pjerus/Temporal-Replay-26-Badge/docs/checkpoints/2026-10-08.md

# Checkpoint 2026-10-08

Parts shopping for driving Rocky's five LEGO Power Functions motors from the spare badge. No code changed; all work is on one page in rocky-robot. Paused for a reboot.

## Completed this session
- `~/ai-dev/rocky-robot/docs/hardware/pf-motor-parts.html`, committed there on `tread-drive` as d530e94, not pushed:
  - "What to buy": four costed options for the motors on hand (three M, one L, one XL) and two shopping lists.
  - Soldered pick, chosen on price: one Adafruit FeatherWing (M and L motors) plus one Pololu Motoron (XL), $44.90 for boards, $70.35 whole build, plus a soldering iron ($17.54 at Anchor).
  - No-soldering build: three Pololu Motorons with screw-down barrier strips, $112.43.
  - Folded table of every part and source checked: SparkFun, Pololu, Anchor Electronics, Jameco, Micro Center Santa Clara, and three Bangkok shops (baht and dollars at 33.3), with soldering tags and riser posts for Technic beams.
  - Parts on hand now lists three Power Functions extension wires (8886).
- Found: no local store has an I2C motor board on the shelf. Jameco boards ship 22 October. Bangkok has no Motoron; Arduitronics has a 290 baht I2C shield.

## Open PRs
None.

## Open issues
None assigned.

## In-flight branches
- `pocket-scanner-phase2` (this repo): de0d811 plus this checkpoint, 7 ahead of `backup` before it, not pushed. Untracked and left alone: `arduino-cli.yaml`, `backups/`.
- rocky-robot `tread-drive`: d530e94, not pushed. The five D11 face-retry files are still uncommitted there, untouched this session.

## Workers/processes to restart on resume
- None from this session: no code changed and nothing was left running.
- The Mac is being rebooted, so anything that was running before stops. Carried over from 7 October: Rocky's brain on the Mac needs a start, and it still lacks the uncommitted D11 retry. The Pi services were not touched.

## Known faults and open questions
- Pat has not chosen between the soldered and the no-soldering build. He has no soldering iron.
- Nothing on the page is tested on hardware: Technic hole fit for the riser posts, the Motoron's motor pins taking push-on jumpers, the XL's current through thin jumper wires.
- Not confirmed: Anchor shelf stock, the badge port's pin order on the ECHO board, whether the Bangkok shield arrives with pins fitted, whether Arduitronics or ThaiEasyElec take walk-in customers.
- Jameco and Micro Center block the headless browser; Firecrawl was used (about 815 credits left, period ends 1 November).

## Next steps
1. Pat picks a build; then order boards (Pololu, and Micro Center if the FeatherWing) and phone Anchor on (408) 727-3693 before the trip.
2. Cut one extension wire and check both halves fit a motor before cutting the other two.
3. Meter-check the badge's 4-pin port, then carry on with the 7 October list (commit D11 retry, restart Rocky, test at the robot).
