pjerus/Temporal-Replay-26-Badge/docs/checkpoints/2026-10-07.md

# Checkpoint 2026-10-07

Rocky's body: the LEGO tank base is driven from rocky-pi through the spare badge. The move-feedback build is done on the Mac but only half deployed to the Pi.

## Completed this session
- On-badge DRIVE app (b83064a) and HELI app for the Syma S107G (1e47bba); both badges carry both apps. Spare = "Rocky IR Tread" (env `echo-drive`), face = "Rocky Face" (env `echo-face-drive`).
- rocky-pi drives the treads: brain → `rocky-body` (8027) → `emotion-bridge` (8026) → spare badge → IR. Proven on the base (forward, early stop, replace).
- Body-feedback design, rev 1: `docs/superpowers/specs/rocky-body-feedback-design.html` (a41de7a). Tread-drive design at rev 3 (f183a66).
- Feedback build, all on `tread-drive` and not pushed:
  - pi-arduino-face-emotions: 4be09ac, 73c4b83 (move ids, endings, `recent_moves`, `refused`), ec45a3e (BLE deadlines), b8734db (history when the badge is gone), b04b188 (`start_within_ms`). 152 tests pass.
  - rocky-robot: 68e1d6a … b2fa2f8 (`schema: 2`, `senses`, drive passthrough, 409 on refusal). 919 tests pass.
- Tested on the base with the first deploy (4be09ac + 73c4b83 level): finished, stopped and replaced endings all reported correctly.
- Name Flip setting (3a947bb): `name_flip = 1` stops the name screen turning on a badge that senses itself inverted. Flashed to the spare and switched on there; Pat confirmed it reads correctly.
- `~/.rocky/config.toml` has `body_enabled = true`; Keychain item `rocky-pi-body` holds the body key.

## Open PRs
None.

## Open issues
None assigned.

## In-flight branches
- `pocket-scanner-phase2` (this repo): 3a947bb, two commits ahead of `backup` (a41de7a, 3a947bb). Push goes to `backup`, never `origin`.
- `tread-drive` in pi-arduino-face-emotions and rocky-robot: unpushed, unmerged, and the Pi runs them.

## Workers/processes to restart on resume
- **rocky-pi `emotion-bridge` and `rocky-body`** — still on the first feedback deploy (services last restarted 05:46 BST on 2026-10-07). They lack ec45a3e, b8734db, b04b188 and the matching rocky-robot commits. Deploy both together: Pat runs `bash ~/ai-dev/pi-arduino/.superpowers/pi_deploy_feedback.sh` (Claude cannot write to the Pi). A second run reported by Pat changed nothing; cause unknown. Check with `grep -c start_within_ms` in the installed `bridge.py`.
- Rocky Face may need switching off and on after the bridge restarts.
- Rocky Face firmware does not have 3a947bb (not needed unless mounted the same way).
- Rocky (the Mac brain) must not run the new client against the old Pi services; deploy the Pi first.

## Known faults and open questions
- Switch-off test not yet passed: with the old Pi code the bridge hung when the badge dropped and the move was never marked `lost`. Fixed in code, unproven on hardware.
- First move after a cold reconnect is refused (connect about 2.6 s, start limit 1 s). Honest answer, brain can retry.
- Spare's battery reads 0 % or 100 %; neither is trusted.
- A badge with its own Drive app open ignores BLE commands silently; needs a firmware flag.
- The BLE secret is hard-coded in firmware and sent unencrypted.
- HELI: stick and trim directions untested (helicopter battery was flat); sent/failed counter still on screen.
- Design page needs a revision recording the build's corrections (deadlines, `recent_moves`, `refused`, `start_within_ms`).

## Next steps
1. Pat reruns the Pi deploy script; confirm both services restarted and hold the new code.
2. Rerun the switch-off test on the base: expect `lost` / `unreachable` about three seconds after the badge goes off, with the history still readable.
3. Revise the feedback design page, then ask Pat about pushing the three branches.

## 12:08 update

The switch-off test passed on the base, a late-`lost` fault was found and fixed, and all three projects are pushed.

### Completed
- Pi deploy of the feedback build confirmed, then redeployed with the fix. rocky-pi `emotion-bridge` restarted 19:56:36 BST and `rocky-body` 19:56:42 BST on 2026-10-07; both run the merged code below.
- Fault found on the base: a status poll saw the badge gone at 1.9 s but the move stayed `running` until 13.5 s. Fixed in pi-arduino-face-emotions 82fb069 (a move is lost the moment anything finds the badge gone). Intermittent on the old code (a race), so the unit test is the main proof.
- Three chained runs on the fix, four drops, each `lost/unreachable` in the same poll as `reachable=false`. Reconnect moves accepted first try.
- Feedback design page at revision 2 (72fcf41): corrections C1–C6, results table, open points.
- rocky-robot 02384db: Rocky calls his face his face, never a screen (done by the rocky-robot session).
- Merged and pushed: pi-arduino-face-emotions `main` = `tread-drive` = 82fb069; rocky-robot `main` = `tread-drive` = 02384db (fast-forwards, 153 and 919 tests pass). This repo: `pocket-scanner-phase2` pushed to `backup` at 72fcf41, not merged to `main`.
- Manifest checksum committed (5fa52ae).
- `.superpowers/pi_deploy_feedback.sh` (git-ignored) now drops the Pi's Bluetooth links to the badges before restarting the bridge. Untried.

### Open PRs / issues
None.

### In-flight branches
- `pocket-scanner-phase2`: level with `backup`. `main` follows upstream (34 commits this branch lacks, 106 it has); merging is Pat's decision. Never push to `origin`.

### Workers/processes to restart on resume
- None owed. Both Pi services run the pushed code.
- Rocky (the Mac brain) was started before 02384db; restart it to pick up the face wording.
- After any future bridge restart, Rocky Face may need switching off and on unless the new link-drop step in the deploy script works.

### Known faults and open questions
- Rocky's brain does not read the tread report (`BodySense` reads touch and distance only), so a lost move is reported by the body and heard by nobody.
- Brick reports pan and tilt as not homed; poses answer 409 until Pat confirms the joints are at home and `POST /home` is sent.
- Body service caps a move at 5000 ms (`[drive] max_ms`); longer drives are chained moves.
- Earlier items still open: Drive app open on the badge ignores BLE silently; BLE secret hard-coded; spare's battery reading; HELI untested.

### Next steps
1. Have Rocky's brain read `drive` (reachable, `last_move`, `recent_moves`) so it hears a lost or refused move.
2. Home pan and tilt with Pat at the robot.
3. On the next Pi deploy, check whether the link-drop step removes the need to power-cycle Rocky Face.

## 13:20 update

Three more bridge changes went to the Pi, Rocky now feels his legs, and an ESP32 modules research page was written.

### Completed
- Bridge (pi-arduino-face-emotions, `main` = `tread-drive` = adf98f3, pushed): a886e74 (a badge that goes off is reported gone without extra waits: the two slow cases of 7 s and 11 s), adf98f3 (a mood for a badge that is away answers at once). 158 tests pass.
- rocky-robot `main` = `tread-drive` = 85db420, pushed: Rocky feels his legs (2d78087, done by the rocky-robot session). Shown live for legs gone and back. 941 tests pass.
- Pi: both services restarted 21:11:37 / 21:11:43 BST on 2026-10-07 and run adf98f3.
- Deploy script's link-drop step worked once (21:11 deploy, face badge left alone, moods answered).
- Feedback design page at revision 3 (5e9e80c): corrections C7–C9, "later the same evening" table, updated open points.
- ESP32 modules research: `rocky-robot/docs/hardware/esp32-modules.html` (130 modules, 13 function groups, scrolling tree, 11-family table) and `esp32-modules-notes/` (three helper reports, chip and satellite facts). Untracked there; Pat has not reviewed it. Registry has a Research entry.
- New global rule `~/.claude/rules/subagent-sizing.md` (model per agent, Kev for bigger jobs, one-tier upgrades, no sub-spawning), after the research job spent about 20 million tokens on four full-size agents.

### Open PRs / issues
None.

### In-flight branches
- `pocket-scanner-phase2`: 5e9e80c plus this checkpoint, ahead of `backup` (d60a386). `main` still unmerged by choice.

### Workers/processes to restart on resume
- None owed. The Pi runs the pushed bridge and body code.
- Rocky (the Mac brain) was last restarted 12:52 Mac time on 85db420's parent code; restart it if rocky-robot changes again.

### Known faults and open questions
- C7–C9 (slow switch-off fixes, fast face failure) are deployed but untried on the base.
- Rocky not yet seen to hear a move lost while one runs, nor the face moods for legs events.
- Switch-on delay of 10–25 s is unmeasured; likely the badge's start-up before it advertises.
- Arm on the Pi is the pretend controller by intent ("we haven't reached that build phase yet").
- Mood sequences lack the fast-failure short cut.

### Next steps
1. With Pat at the robot: switch Rocky Face off and on (fast face failure), then the tread badge off (expect Rocky to notice within about 3 s).
2. Pat reads the ESP32 modules page; trim or deepen, then commit it in rocky-robot and link it from the parts guide. Follow-up research under the sizing rule.
3. Time the switch-on delay: badge menu appearing versus `reachable` turning true.

## 13:22 update

Only change since the update above: everything is pushed.

### Completed
- `pocket-scanner-phase2` pushed to `backup` at 1a17062 (design page revision 3, checkpoint).

### Open PRs / issues
None open by me.

### In-flight branches
- `pocket-scanner-phase2`: level with `backup` apart from this note. `main` (f140554) still unmerged by choice.
- Untracked and left alone: `arduino-cli.yaml`, `backups/`.

### Workers/processes to restart on resume
- None. No code changed since the Pi's 21:11 BST restart.

### Next steps
Unchanged: the three in the update above.

## 16:07 update

### Completed
- `rocky-body-feedback-design.html` is at revision 4 (8f611f1, c9341ac, 5a07617, 5b52422, 97476a2). It records the rocky-robot session's results for C7 to C9 on the base, about 22:25 to 22:47 BST (14:25 to 14:47 Mac time):
  - Face badge off and on (C9): pass. Moods failed in 0.05 to 0.14 s while off; first good one after switch-on took 0.35 s.
  - Tread badge off mid-move (C6 to C8): pass, three times. Each lost move was marked lost in the report that first showed the badge gone; slowest report 1.17 s; no 7 s or 11 s silence.
  - One miss: at switch-off 3 the legs-gone mood did not reach the face badge (a Bluetooth "unlikely error" on the face badge at that moment).
  - Switch-on delay: skipped at Pat's word, still unmeasured.
- Decision D11 (Pat: "sure retry", then "yes your recommendations ok"): a face command the badge missed is sent again every 2 s for up to 10 s, dropped when a newer face is asked for, for every face send.
- D11 is built in `~/ai-dev/rocky-robot`, branch `tread-drive`, **uncommitted** at Pat's word ("Not right now"): `rocky/badge/sink.py`, `rocky/badge/install.py`, `rocky/config.py` (`badge_retry_every_s`, `badge_retry_for_s`), `tests/test_badge_sink.py`, `tests/test_badge_install.py`. Four new tests, each seen failing first; full suite 945 passed.

### In-flight branches
- `pocket-scanner-phase2`: 6 ahead of `backup/pocket-scanner-phase2` before this checkpoint, not pushed.
- rocky-robot `tread-drive` at c1e30e9 plus the uncommitted D11 change above.

### Workers/processes to restart on resume
- Rocky's brain on the Mac: started about 14:25 from rocky-robot c1e30e9, so it runs the old `rocky/badge/sink.py` with no retry. Restart it after the D11 change is committed. Whether it is still running was not checked.
- Pi bridge: said to be on adf98f3, not checked this session. Nothing changed on the Pi.
- The tread badge was switched off when the last test run ended (14:46 Mac time).
- The rocky-robot session that ran the tests has closed.

### Known faults and open questions
- The face moods for legs gone and back were read from the face badge's state, not confirmed by eye.
- One move sent in the same instant the badge dropped took 2.05 s to be turned away; the Pi log for 22:42:36 to 22:42:39 BST on 7 October would show why.
- The face badge reported battery 100 before it was switched off and 0 after.
- The Pi's bridge commit was assumed, not confirmed.

### Next steps
1. Ask Pat whether to commit the D11 change in rocky-robot; then restart Rocky's brain.
2. At the robot: switch the tread badge off a few times and check the scared mood reaches the face badge even after a face error; have Pat confirm the moods by eye.
3. Time the switch-on delay: from the badge's menu appearing to the treads moving.
