pjerus/Temporal-Replay-26-Badge/docs/checkpoints/2026-10-05.md

# Checkpoint 2026-10-05

Badge = Rocky Robot's face. rocky-pi hosts the emotion bridge; the Mac brain (rocky-robot) sends moods through it.

## Completed this session
- Display identified and documented: 2.42" 128×64 SSD1309 OLED, module DST-018 (4d8feb4, b099c7a). Headline docs say ECHO/WROOM-1; MINI-1/XIAO is DELTA only.
- Repo de-nested from `upstream/` to `~/ai-dev/pi-arduino`. Phase 2 apps committed (f8571f6).
- Spike: rocky-pi drives the badge over BLE and the NXT over classic BT at the same time. The NXT motor is on port A (works; the old "A jammed" note is stale). Ultrasonic sensor on input 1.
- Firmware e4b0839: frame flag bit2 `kFlagShowFace` brings up the robot face screen (it waits for a running app or Doom). Every BLE write counts as activity, so a battery badge doesn't deep-sleep. Flashed to the badge (echo-dev) and verified live.
- face-emotions (separate repo): injectable HTTP transport f24a272, BLE keep-alive + `EMOTION_BRIDGE_HOST` f57a1a3, `show_face` 16fb4b4. 42/42 tests.
- rocky-pi: bridge installed as systemd `emotion-bridge` (enabled, port 8026, LAN, API key in `~/.config/emotion-bridge/env`). Code in `~/emotion-bridge`.
- coderef: emotion-client-py v4 + v5, emotion-frame v3, emotion-consumer v2.
- All three repos pushed (this one to the `backup` fork).

## Open PRs
- None.

## Open issues
- None assigned.

## In-flight branches
- `pocket-scanner-phase2` @ e4b0839, pushed to backup. Merging to main is still deferred (34-commit reconciliation).
- Uncommitted: `firmware/initial_filesystem/manifest.json` (build artifact), `arduino-cli.yaml`, `backups/`. Left alone on purpose.

## Workers/processes to restart on resume
- None pending. The rocky-pi `emotion-bridge` runs 16fb4b4 (redeployed and restarted). The badge runs e4b0839.
- If the badge ever sleeps while the bridge is retrying, BlueZ can wedge ("Operation already in progress"). Rebooting rocky-pi clears it. Don't kill `bluetoothctl scan` with `timeout`; that is what wedged it this session.

## Next steps
1. rocky-robot session (Pat must say it there): build the heartbeat mood, pass `show_face=True` (take emotion-frame v3 with client v5), run a full voice turn, commit.
2. Put the badge back on Rocky and check the Pi reaches it from there (it is on the Mac's USB now).
3. Bridge fail-fast: while the badge is unreachable, requests queue behind BLE connects instead of returning a quick 502. Add port 8026 to the local-dev-hosting registry. Backlog: Jarvis STT on the Pi.
