pjerus/Temporal-Replay-26-Badge/docs/pocket-scanner/checkpoints/2026-05-11.md

# Session checkpoint — 2026-05-11

Pocket Scanner Phase 1 shipped end-to-end. Hackable handheld scanner platform built on a Temporal Replay 26 conference badge.

## Completed this session

- **Identified hardware:** Temporal Replay 26 badge (ESP32-S3-WROOM-1, 16MB flash, 8MB octal PSRAM, 8×8 IS31FL3731 LED matrix, LIS2DH12 IMU, SSD1309 OLED, joystick, 4 buttons, IR, WiFi, BT, 1000mAh LiPo). Two units; board #1 is our dev platform, board #2 stays factory.
- **Cloned upstream firmware** (`Architeuthis-Flux/Temporal-Replay-26-Badge`) at tag `0.2.4` into `upstream/`, branch `pocket-scanner-phase1`.
- **Installed toolchain:** PlatformIO 6.1.19 + esp-idf + vendored MicroPython v1.27.0 sources (includes `bluetooth`, `socket`, `network` modules — Phase 2 BLE scan should be reachable from MicroPython without C-side firmware work).
- **Forked firmware:** 4 commits on `pocket-scanner-phase1` branch since `0.2.4`. Menu: 24 curated + 6 dynamic → 12 curated + 6 dynamic. Build size: 67.5% → 60% (~290KB saved + 4MB FATFS from DOOM WAD removal).
- **Phase 1 demo verified on hardware:** joystick moves a cursor on the 8×8 matrix, CONFIRM cycles brightness, IMU face-down dims output, BACK exits cleanly.
- **Restored board #1 from factory bin earlier in session** (`backups/firmware-v0.2.4/factory_echo_16MB.bin`, 16MB full-chip image, SHA `1fc5b04c...`); board now runs our fork instead of factory.

## Open PRs / issues

None. Neither repo has a remote configured.

## In-flight branches

**Outer repo** (`~/temporal-badge-scanner/`):
- `main` @ `1a2ae35` — docs only (spec, plan, README, checkpoint). 4 commits. Clean.

**Inner repo** (`upstream/`):
- `pocket-scanner-phase1` @ `00a76a5` — our fork. 4 commits ahead of `0.2.4`. One working-tree file shows as modified (`firmware/initial_filesystem/manifest.json`, regenerated pre-build — ignore or commit separately if intentional changes accumulate).
- `main` @ `f140554` (tracking upstream `origin/main`) — untouched, useful if we ever want to pull newer upstream commits.

## Local-only quirks (do not lose these)

- `upstream/firmware/wifi.local.env` is **skip-worktree** (placeholder creds: SSID `pocket-scanner-dev`, URL `http://127.0.0.1:1`). Real conference creds were committed by upstream — we don't want either form pushed if we ever add a remote.
- `upstream/firmware/src/infra/BuildWifiConfig.generated.h` is **skip-worktree** (auto-regenerated from wifi.local.env on every build, noisy otherwise).
- `upstream/.git/info/exclude` has `firmware/lib/micropython_embed/` (vendored MicroPython sources, regenerated by `ignition/setup.sh`).

## Workers / processes to restart on resume

None. No daemons or long-lived workers were started this session. The "worker" is the badge itself, currently running our flashed `pocket-scanner-phase1` firmware. To re-flash after code changes:

```sh
cd ~/temporal-badge-scanner/upstream/firmware
~/.platformio/penv/bin/pio run -e echo-dev -t upload --upload-port /dev/cu.usbmodem2101
# add `-t uploadfs` after `-t upload` if initial_filesystem/ changed
```

Always use `~/.platformio/penv/bin/pio` directly — system `pio` shim points to wrong Python.

## Next steps when resuming

1. **Phase 2: add the first scanner screen.** Easiest win is BLE Scan (live list of nearby BLE devices with name + MAC + RSSI). MicroPython `bluetooth` module is vendored and available. Add as a new screen in `/apps/scanner/main.py` selectable from a menu the existing demo currently lacks.
2. **Re-read upstream's existing IR PLAY screen** (`firmware/src/screens/`) — we kept it; it's a "universal remote, sniffer, TV-B-Gone, IR mini-games" entry. Likely a useful reference (or even reusable) for our planned IR capture/replay scanner screen.
3. **Decide on board #2.** Currently factory v0.2.4 and untouched. Options: leave as-is (conference memento + restore reference), or flash it with the same fork so we have two scanners (enables future Phase 2 two-badge ESP-NOW projects).

## Pointers

- Spec: `docs/superpowers/specs/2026-05-11-pocket-scanner-design.md`
- Plan: `docs/superpowers/plans/2026-05-11-pocket-scanner.md`
- Project README: `README.md` (build/flash/restore quickref)
- Upstream CLAUDE.md: `upstream/CLAUDE.md` (auto-loaded; contains pin map, NVS namespaces, gotchas)
- Factory restore: `../backups/firmware-v0.2.4/factory_echo_16MB.bin`

## 21:40 update — Phase 2 BLE scan plumbing in, scan not populating

Phase 2 BLE scan plumbing complete on `pocket-scanner-phase2` (4 commits ahead of `pocket-scanner-phase1`). Firmware + filesystem flashed. Hardware test: BLE Scan screen opens cleanly but the device list does not populate — `n=N` stays at 0.

### Completed this session

- **Plan written:** `docs/superpowers/plans/2026-05-11-pocket-scanner-phase2-ble-scan.md` (outer repo, commit `418fe1e`).
- **Cut Phase 2 branch:** `pocket-scanner-phase2` off `pocket-scanner-phase1` head (`00a76a5`).
- **Refactored scanner app:** Phase 1 demo extracted to `apps/scanner/demo.py`, `apps/scanner/main.py` rewritten as a launcher menu, new `apps/scanner/ble.py` for the BLE screen.
- **Found NimBLE not in build:** MicroPython's `bluetooth` extmod is config-enabled (`MICROPY_PY_BLUETOOTH=1`) but the build excludes `extmod/modbluetooth.c`, `extmod/nimble/*`, and the NimBLE HAL headers were never vendored. `import bluetooth` fails at runtime.
- **Built C-side BLE bridge** (commit `b7d90d4`) using arduino-esp32's bundled `BLEDevice` / `BLEScan`:
  - `src/ble/BleScan.{cpp,h}` — 32-entry device table keyed by MAC, mux-protected callback, lazy controller init, never deinits.
  - `src/micropython/badge_mp_api/mp_api_ble.cpp` + HAL shims + 5 `MP_QSTR_ble_scan_*`.
  - `apps/scanner/ble.py` rewritten to call `badge.ble_scan_start/stop/count/get/prune`.
  - `platformio.ini` `build_src_filter` now adds `+<ble/BleScan.cpp>` (the rest of `ble/` stays excluded — it's gated on `BADGE_ENABLE_BLE_PROXIMITY`).
- **Build size:** 60.4% → 66.0% flash (BT library + new code, ~230 KB).

### Open follow-ups

- **BLE scan returns no devices on hardware.** `ble_scan_start()` returned 0 (success path), screen renders `BLE n=0` indefinitely. Either `BLEDevice::init()` silently fails, the controller comes up but the callback never fires, or callbacks fire but adv parsing drops everything. Needs serial-log inspection — `BleScan.cpp` already prints `[blescan] init OK` / `[blescan] init failed` on first `start()`. Sample serial while the BLE Scan screen is open:
  ```sh
  stty -f /dev/cu.usbmodem2101 115200 cs8 -cstopb -parenb
  timeout 20 cat /dev/cu.usbmodem2101 | grep -E "blescan|ble\]|panic|abort"
  ```
  If `init OK` is printed but no advs reach the callback, suspect WiFi-coexistence DRAM contention (placeholder WiFi may still be allocating) — try forcing `WiFi.mode(WIFI_OFF)` before `ensureInitialised()`. If `init failed`, check `largest=` heap number in the log.
- **Bird game crash (task #2):** Instrumented `apps/scanner/.../fa_engine.py` `main()` to print end-state to serial (working-tree change, not yet committed — see "Local-only quirks" below). User has not produced a serial trace yet. Next session: capture serial while reproducing the crash to learn which `reason` fires.

### Local-only quirks (do not lose these)

- **`lib/micropython_embed/src/genhdr/qstrdefs.generated.h` hand-patched** with our 5 new `ble_scan_*` QSTRs (file is gitignored — generated by `micropython/setup_arduino_embed.sh`). Re-running setup will regenerate the file and pick up the QSTRs automatically because they're referenced in the committed `modtemporalbadge.c`. But on this machine, if the file is regenerated by anything else (e.g. a fresh `setup_arduino_embed.sh` run that fails partway), the manual entries are lost and the build will break. Hash format: `QDEF1(MP_QSTR_<name>, <djb2-hash mod 256>, <len>, "<str>")`.
- **`firmware/initial_filesystem/apps/flappy_asteroids/fa_engine.py` has a working-tree-only debug print** at `main()` that dumps `FA reason=…` to serial when a game ends. Either commit (and remember to remove later) or `git checkout` once the bug is diagnosed.
- Same Phase 1 manifest.json + community_apps.json regenerator drift as before — leave uncommitted.

### Branches

**Outer repo** (`~/temporal-badge-scanner/`):
- `main` @ `418fe1e` — added Phase 2 plan. Clean.

**Inner repo** (`upstream/`):
- `pocket-scanner-phase2` @ `b7d90d4` — 4 commits ahead of `pocket-scanner-phase1`. Working tree shows the manifest/community_apps drift + the gitignored qstrdefs patch + the unstaged `fa_engine.py` debug print.
- `pocket-scanner-phase1` @ `00a76a5` — untouched.
- `main` @ `f140554` — untouched.

### Workers / processes to restart on resume

None on the host. The badge itself is currently flashed with the Phase 2 firmware + filesystem (commit `b7d90d4` + the unstaged `fa_engine.py` debug print). The qstrdefs patch is baked into that firmware build. If the badge is reflashed from a fresh source checkout without re-running `setup_arduino_embed.sh`, BLE will silently disappear (the QSTRs won't be in the regenerated qstrdefs).

To re-flash after code changes:
```sh
cd ~/temporal-badge-scanner/upstream/firmware
~/.platformio/penv/bin/pio run -e echo-dev -t upload   --upload-port /dev/cu.usbmodem2101   # firmware (C++ changed)
~/.platformio/penv/bin/pio run -e echo-dev -t uploadfs --upload-port /dev/cu.usbmodem2101   # filesystem (.py changed)
```

### Next steps when resuming

1. **Diagnose BLE scan returning n=0.** Run the serial-grep above with the BLE Scan screen open. Decide based on `[blescan]` line whether init failed (heap/coexistence) or callback isn't firing (BT controller / scan params).
2. **Pull the bird-game crash trace.** Restart the 60s serial capture and have the user reproduce; grep for `FA reason=`. Then fix the underlying bug in the `flappy_asteroids/` source.
3. **Bake the QSTRs properly.** Once everything is working, run `micropython/setup_arduino_embed.sh` to regenerate `qstrdefs.generated.h` from source-of-truth so the manual patch isn't load-bearing.

### Pointers

- Phase 2 plan: `docs/superpowers/plans/2026-05-11-pocket-scanner-phase2-ble-scan.md`
- New C++ files: `upstream/firmware/src/ble/BleScan.{cpp,h}`, `upstream/firmware/src/micropython/badge_mp_api/mp_api_ble.cpp`
- Existing iBeacon scanner (reference, not used): `upstream/firmware/src/ble/BleBeaconScanner.cpp` — gated on `BADGE_ENABLE_BLE_PROXIMITY`

## 22:00 update — two launcher-import fixes, BLE init still unverified

After the 21:40 checkpoint we tried to diag the "n=0" report and surfaced two unrelated launcher bugs in front of the actual BLE init question. Two fixes shipped, BLE init logs still uncaptured.

### Two bugs found and fixed (commits ahead of `b7d90d4`)

- `ca7b233` **`fix(scanner): add /apps/scanner to sys.path so launcher can import ble/demo`** — `main.py` was doing lazy `import ble` / `import demo` but the badge runtime doesn't put the app's directory on `sys.path` automatically. Same idiom flappy_asteroids/main.py uses. Symptom on hardware: `BLE Scan failed: no module named 'ble'`.
- `d8be53b` **`fix(scanner): from badge import * in ble.py + demo.py for native globals`** — sub-modules don't inherit the bare-global injection that the app entry point gets. `ble.py` was calling `oled_*`, `button_pressed`, `ble_scan_start`, etc. without importing them. Symptom on hardware: `NameError: ble_scan_start`. Same fix applied to `demo.py` (latent — never tested but would have failed the moment Demo was launched from the new launcher).

### Still unverified

- **BLE controller init has never actually run** in any of our hardware tests so far — every attempt died in Python before reaching `BleScan::start()`. With `d8be53b` flashed, the next BLE Scan launch should surface the real init outcome. The serial-grep above (`stty ... | grep blescan`) is the diagnostic.
- **Demo screen** has not been re-verified after the launcher refactor + the `from badge import *` fix. Should still work, but worth a 30 s sanity check.

### State

- Branch `pocket-scanner-phase2` now 6 commits ahead of `pocket-scanner-phase1`. Working tree shows the same Phase 1 manifest/community_apps drift + the unstaged `fa_engine.py` debug print + the gitignored qstrdefs hand-patch.
- Badge currently flashed with: firmware @ `b7d90d4` (BLE C bridge), filesystem @ `d8be53b` (fixed launcher).

### Next steps when resuming

1. Confirm BLE Scan now opens cleanly, capture `[blescan] init OK` / `init failed` from serial (`stty -f /dev/cu.usbmodem2101 115200 cs8 -cstopb -parenb; timeout 30 cat /dev/cu.usbmodem2101 | grep -iE 'blescan|wifi|panic|largest'`).
2. If `init OK` but `n=0`: add a Serial.printf for `s_advCount` from the loop side to prove callbacks fire (or don't). If callbacks aren't firing, suspect the active-scan param or wantDuplicates interaction.
3. If `init failed`: read the `largest=` heap number — anything below ~32 KB and you're at the BleBeaconScanner's documented init floor; need the same WiFi-off + memory-anchor song-and-dance.
4. Sanity-check Demo screen still works.
5. Bird game crash trace (still task #2, still blocked on a serial capture during repro).

## 22:15 update — qstr pool sort invariant was the actual blocker

The `from badge import *` fix at 22:00 didn't actually surface `ble_scan_*`. Root cause: I appended our 5 new QDEF1 entries at the end of `lib/micropython_embed/src/genhdr/qstrdefs.generated.h` rather than alphabetically. The second qstr pool (`mp_qstr_const_pool` in `lib/micropython_embed/src/py/qstr.c`) is declared `is_sorted = true`, so `qstr_find_strn` does a binary search over it. Binary-searching for "ble_scan_start" in an out-of-sort pool returns 0 → MicroPython interns our identifier as a fresh dynamic qstr at a *different* id than the locals_dict key registered in `modtemporalbadge.c` → the lookup misses entirely. `from badge import *` couldn't surface the function because the dict entry's qstr id no longer matched the parser-interned qstr id.

### Fix shipped

- One-line patch in `lib/micropython_embed/src/py/qstr.c`: `is_sorted: true → false` for the second pool. Linear search instead of binary; ~few µs slower per parse-time qstr lookup, totally fine. Also gitignored — same caveat as the qstrdefs hand-patch (re-running `setup_arduino_embed.sh` regenerates it).
- Firmware rebuilt + reflashed with this change.

Filesystem unchanged from the 22:00 state (`d8be53b`); badge user has not yet retested BLE Scan after this firmware reflash.

### Better long-term fix (deferred)

Re-run `micropython/setup_arduino_embed.sh` to regenerate `qstrdefs.generated.h` with `ble_scan_*` in correct sort position. That removes both the hand-patched qstrdefs *and* the `is_sorted=false` regression. Alternatively, ship a third qstr pool of just our additions (`is_sorted: false` on that pool only) so the existing 700-entry pool keeps its fast lookup.

### Next steps when resuming (revised)

1. **Retest BLE Scan** with current firmware. Should now actually open and call `ble_scan_start()` — at which point the original "n=0" investigation can resume with the `[blescan] init OK / failed` serial logs.
2. Sanity-check Demo screen.
3. Bird-game crash trace.
4. Eventually: run setup_arduino_embed.sh to bake the QSTRs properly and undo the `is_sorted=false` workaround.

## 22:25 update — Phase 2 BLE scan confirmed working on hardware

User confirmed "working now" after the qstr-pool fix flashed. Phase 2 MVP is done.

### Remaining tomorrow

- Bird-game crash trace (still need a serial capture during repro).
- Eventually re-run `setup_arduino_embed.sh` to bake the QSTRs cleanly and undo the `is_sorted=false` workaround.

## 22:50 update — observations + idea backlog

- **Bird-game "crash" closed.** Fixed by separating into Both/Asteroids/Flappy modes via `pick_mode()` (commits `1363777` + `42f9027`). Not a code bug; the dual-screen design surprised the user.
- **Synth app reportedly silent.** Sound path is `badge.tone(freq, dur, duty)` → `CoilTone::tone()` → vibration-motor PWM coil whine. Echo defines `BADGE_HAS_HAPTICS` so the real driver is compiled in (not the no-op stub). No speaker — sound is barely-audible motor coil whine, narrow band. Most likely the synth IS playing but it's too quiet to notice unless held close to the ear in a silent room. Verify by calling `badge.tone(440, 1000, 30)` from REPL; if still silent, check `Haptics::enabled()` (the motor master switch — badge settings may have disabled it).

## 23:15 update — two new MicroPython apps shipped (LED Demos + Billboard)

- **`/apps/leddemos/`** (commit `f036103`) — launcher with Fire / Plasma / Matrix Rain. Each uses per-pixel `led_set_pixel(x, y, brightness)` over the full 8×8 to fake antialiasing/depth that the monochrome matrix can't otherwise express. Fire = cellular automaton, Plasma = dual sine field with 256-entry lookup, Rain = per-column random-speed drops with fading trails.
- **`/apps/billboard/`** (commits `5085ce4`, `33bc50b`) — rave-style name tag. Reads name from `/apps/billboard/name.txt` (defaults to "BADGE"), picks the largest u8g2 font that fits via `oled_text_width()` measurement (Spleen 32x64 → 16x32 → 12x24 → ...), runs one of 5 effects (Scroll, Strobe, Pulse, Marquee, Sparkle) or auto-cycles. Synced eye-candy on the LED matrix per mode (column sweep / fill-strobe / breathing / chase border / sparkle decay).

### Bugs found while shipping these

- **Launcher pattern requires explicit sys.path**: any multi-file app in `/apps/<name>/` whose `main.py` does `import siblingmodule` needs `sys.path.insert(0, "/apps/<name>")` first. The badge runtime doesn't put the app dir on sys.path automatically.
- **Sub-modules don't inherit bare-global injection**: only the entry `main.py` gets `oled_*`, `button_pressed`, `BTN_*` injected as bare globals. Sibling modules must `from badge import *` themselves.
- **`button_pressed` is edge-triggered** — once a press is consumed by the inner loop, the outer-loop re-check returns False. Fix: have inner loops return a sentinel (`EXIT_BACK` / `EXIT_NEXT`) so the caller dispatches without re-querying.
- **`time.ticks_add` may not exist** on this MicroPython port — use `badge_app.ticks_add` which has a fallback.

(All four lessons are now baked into the new apps; reference for the next app you add.)

### Status

- Phase 2 BLE scan: working ✓ (commit `b7d90d4` + downstream fixes)
- flappy_asteroids "crash": resolved by mode separation (commits `1363777` + `42f9027`)
- Synth: hardware-side OK on Echo (sound = motor coil whine, very quiet — held to ear test recommended)
- LED Demos + Billboard: shipped, working on hardware

## 23:55 update — published to personal github + history scrubbed

Both repos pushed to pjerus' personal GitHub:

- **Inner (firmware fork):** https://github.com/pjerus/Temporal-Replay-26-Badge — branch `pocket-scanner-phase2`. Upstream Architeuthis-Flux remote was removed entirely from the local clone, so accidental pushes to upstream are now impossible. `origin` is the personal fork.
- **Outer (project repo):** https://github.com/pjerus/temporal-badge-scanner — branch `main`. New repo, no relation to upstream.

### Pre-push security audit + cleanup

Found and fixed:
- All commits authored by `pat.jerus@gmail.com` rewritten to GitHub's noreply alias `12172455+pjerus@users.noreply.github.com` via `git filter-branch --env-filter`. Inner branch fully purged (verified via `git log pocket-scanner-phase2 --pretty=format:"%ae" | sort -u` — only the noreply + upstream contributors remain). Outer branch fully purged.
- Local absolute paths `/Users/pat/...` scrubbed from every commit on outer `main` via `git filter-branch --tree-filter` doing sed replacement to `~/`. Verified `git grep '/Users/pat'` returns zero hits across the rewritten history.
- Both branches force-pushed (inner `9f6a645` → `240613d`, outer `8f858c3` → `2ada214`).

Left alone:
- `firmware/wifi.local2.env` — placeholder/template values, not real credentials. (Pre-existing tracked file, inherited from upstream's `0.2.4` tree.)
- Upstream HMAC key in `BleBeaconScanner.cpp` — already public in Architeuthis-Flux's repo, not introduced by us.
- The pre-rewrite SHAs (`9f6a645`, `8f858c3`, all the `feat(scanner)` and `docs:` SHAs that appear in earlier sections of this checkpoint) remain accessible by SHA in GitHub's reflog cache for ~90 days. User accepted this risk.

### Local git config now in effect

Both repos: `user.email = 12172455+pjerus@users.noreply.github.com`, `user.name = Pat Jerus`. Future commits in these repos auto-pick this up; no further action needed.

### Resume notes

- The badge is currently flashed with firmware @ pre-rewrite `b7d90d4` plus filesystem @ pre-rewrite `33bc50b`. SHAs on disk don't match the rewritten history, but that's harmless — the binary content is identical, only the commit metadata changed.
- Working-tree drift in inner repo (manifest.json, community_apps.json, qstrdefs.generated.h, qstr.c) is the same regenerator/hand-patch state as before. Leave uncommitted.
