pjerus/Temporal-Replay-26-Badge/docs/superpowers/specs/rocky-body-feedback-design.html

# What Rocky's body tells his brain

Started 2026-10-06 · Revision 4 (2026-10-07) — adds the first results for C7 to C9 on the base with Rocky running (the switch-on delay was skipped and is not yet measured); revision 3 (2026-10-07) added three later bridge changes (C7 to C9) and Rocky's brain reading the tread report; revision 2 (2026-10-07) recorded what the build changed and the results on the base · status: stage 1 built, tested on hardware and pushed; C7 to C9 deployed and passed on the base, with one face mood missed · follows on from Driving the treads from rocky-pi

## In one paragraph

The body service on rocky-pi already answers in JSON, and Rocky's brain already reads it once a second. What it lacks is outcomes. A drive command answers "accepted" and nothing more, and the report mixes what was asked for with what was measured. This design gives every move a number and a stated ending, separates commanded from measured, and puts every sensor reading into one common shape, with empty slots ready for the sensors we have not wired in yet.

## What the build changed (revisions 2 and 3)

Stage 1 was built on 6 and 7 October and tested on the tank base. The design held, but the build added nine things this page did not have. C1 to C6 came with revision 2; C7 to C9 came later the same evening, from watching Rocky run against the Pi. Each is reflected in the sections below.

| Correction | Why it was needed
C1 | Every Bluetooth operation has a deadline: 3 s for a read or write, 10 s for a connect. Past it the badge counts as unreachable and the link is dropped. | A badge that is switched off leaves the link half-open: nothing answers and nothing fails. Without a deadline the bridge hung and the move was never marked lost.
C2 | A badge known to be gone is answered from memory. Status requests and new moves come back "unreachable" at once, while one attempt to reach the badge runs behind them. | Reaching for a missing badge can take as long as a connect. The brain polls once a second and must not wait for that.
C3 | recent_moves: the report carries the newest 8 moves, newest first, not only last_move. It stays readable while the badge is unreachable. | A new move overwrites last_move, so a reader that polls slowly could miss how the one before ended.
C4 | refused is a real ending. The badge's status carries two flags, low_memory and rejected. A move the badge will not take is numbered, ends refused with that flag as the reason, and the body service answers 409. | Revision 1 drew "refused" but had no source for it.
C5 | start_within_ms: the caller says how long it will wait for the move to start. If the badge is not ready by then, the move does not start and gets no number. | A move must not begin after its caller has given up waiting to hear that it did. A cold connect takes about 2.6 s; the body service waits 1 s.
C6 | A move is lost the moment anything finds the badge gone, and its resend loop is cancelled then. | Found on the base on 7 October: a status poll noticed the drop at 1.9 s, but only the move's own resend could end the move, and it queued behind the reconnect attempt. The report said "unreachable" and "running" together until 13.5 s.
C7 | Letting go of a dead link runs behind the caller. The operation that timed out reports "unreachable" after its one deadline; only the next connect waits for the old link's disconnect. | Seen on the Pi: 7 s with no answers before the badge was reported gone. The read waited 3 s, then the disconnect of the dead link took up to 3 s more, with every poll queued behind it.
C8 | A status read does not start a connect. If Bluetooth has already reported the link down, GET /drive answers "no link to the badge" at once and the connect is left to the attempt running behind. | Seen on the Pi: 11 s with no answers. The status read had started a fresh connect, which is allowed 10 s.
C9 | A mood for a badge that is away answers at once, as a status read does (C2, C8), and starts the attempt behind it. That attempt now uses a read every badge offers, so a mood-only badge is found again. | Rocky's mood sends waited out a connect while the face badge was off and ran past his 5 s limit. Pat, 7 October: "let's do fast face failure."

### Results on the base, 7 October

Each run chained a slow move every 4 s for a minute while the report was polled about twice a second. Pat switched the tread badge off, and sometimes on again, during the run.

Run | Bridge code | Badge seen gone at | Move marked lost at | Result
A | before C6 | 1.9 s | 13.5 s | Late by 11.6 s. No hang; slowest report 1.6 s.
B | before C6 | 1.7 s | 1.7 s | On time: the fault was a race, not constant.
1 | with C6 | 2.0 s and 47.5 s | same poll, both times | Pass. Slowest report 0.5 s.
2 | with C6 | 19.2 s | same poll | Pass. First move after switching back on accepted.
3 | with C6 | 26.7 s | same poll | Pass.

Across every run: no report failed, the move history stayed readable while the badge was off, moves sent to a missing badge were refused in about 0.1 s without getting a number, each replaced move ended replaced/new_move, and the badge took a new move once it was back. Finished, stopped and replaced endings had already been checked on the base on 6 October.

Because run B came out clean on the old code, the three clean runs do not prove C6 by themselves. The stronger proof is the bridge test that failed before the fix and passes after it.

### Later the same evening

What | Evidence | Standing
Rocky's brain reads the tread report (rocky-robot 2d78087) | With no script and no moves: badge on, "I feel my legs"; badge off, "I do not feel them. The signal is quiet."; badge on again, he feels them. One wrong answer first, fixed by blunter wording of the note he is given. | Shown live for legs gone and back. Not yet shown: the face moods for each event, and a move lost while Rocky is running.
Switching off is sometimes noticed slowly | Pi log: no answers for 7 s (20:38:45 BST) and 11 s (20:54:45 BST) before the first "unreachable". Rocky's 3 s report timeouts fell in such gaps. | C7 and C8, deployed 21:02 BST. Each has a test that failed before and passes after. Tried on the base later that night (results below). Expected: about 3 s at worst for a half-open link, at once when the link is known down.
Moods hang while the face badge is away | Rocky's log: one 5 s timeout at 21:04 BST while Pat restarted the face badge; the Pi logged no answer in that window. | C9, deployed 21:11 BST, tested on the Mac. Tried on the base later that night (results below).
The deploy drops the Pi's Bluetooth links before restarting the bridge | 21:11 BST deploy: Pat left the face badge alone, two moods answered within a minute, and the tread badge was back after 8 s. | Worked once. The power-cycle after a deploy is a fallback now, not a step.
Switching on is slow (10 to 25 s, loosely timed) | The bridge retries a gone badge back to back while anyone polls, so the wait is not a retry interval. The Pi log shows the changeover itself takes one poll. | Unmeasured. Most likely the badge's own start-up before it advertises. To split it: time from the badge's menu appearing to reachable turning true.

### C7 to C9 on the base, with Rocky running (revision 4)

Run by the rocky-robot session from about 22:25 to 22:47 BST on 7 October, with Pat at the badges' switches. Rocky's brain ran on the Mac from tread-drive c1e30e9, which includes 85db420 and 2d78087. The Pi was said to be on bridge adf98f3; that was not checked again here. A script on the Mac polled the body report every 0.25 s and the face badge's state every 0.5 s, and listened on Rocky's face websocket to see when his brain reacted. Times are BST, converted from the Mac's clock.

Face badge switched off and on (C9): pass. No mood waited on a connect; Rocky's limit is 5 s.

Step | When | What the mood request did
Face on, before | | Answered in 0.23 to 0.46 s.
Switched off | Last good mood 22:40:48.8; first failure 22:40:50.87 | Failed in 0.07 s: 502, "no link to the badge".
While off | 13 failures | Each failed in 0.05 to 0.14 s. The first 5 said "no link to the badge"; from 22:41:01.4 the other 8 said "no connection to the badge within 10 s".
Switched on | First good mood 22:41:18.4 | Answered in 0.35 s, then as before. That is 27.5 s after the first failure, which includes however long the badge was left off.

Tread badge switched off mid-move (C6 to C8): pass, three times in one 5-minute run. Moves of 5 s at speed 1, forward then back, were sent about every 4.5 s.

Switch-off | Report first showed the badge gone | Move marked lost | Rocky's brain reacted | Face badge | Switched back on
1 | 22:42:37.65 | Move 12, same report | 22:42:37.65 | Scared 0.8 at 22:42:38.7, back to his resting mood after 6 s | Reachable 22:42:53.93, 16.3 s after gone. Happy at 22:42:55.3. Move 13 accepted first try, 22:42:55.9.
2 | 22:43:07.49 | Move 15, same report | 22:43:07.50 | Scared at 22:43:08.6 | Reachable 22:43:29.58, 22.1 s after gone. Happy at 22:43:30.3. Move 16 accepted first try, 22:43:31.3.
3 | 22:44:02.81 | Move 22, same report | 22:44:02.77 | Not shown. The mood send failed with a Bluetooth error on the face badge. | Left off until the run ended at 22:46:42.

Across the run: no report failed and the slowest took 1.17 s. Every lost move was already marked lost in the report that first showed the badge gone. 47 moves sent while the badge was off were turned away (503, treads unreachable) and none got a number; each one sent after a gone report took 0.08 to 0.34 s. One took 2.05 s: at switch-off 1 it was sent at about 22:42:36.73, within 0.05 s of the report request that first found the badge gone, so nothing yet knew the badge was away. It was the only move in the run sent before a gone report. The exact switch-off instants were not recorded, so "noticed within" is bounded only by the gap between the last good report and the first gone one, about 1.3 s at worst. No 7 s or 11 s silence appeared.

The miss at switch-off 3: Rocky logged "badge face unavailable" with a Bluetooth "unlikely error" from the face badge, and the script's own read of the face failed at 22:44:01.5, 1.3 s before the legs were reported gone. The face read normally again by 22:44:05.6. One similar single failed read came at 22:42:09.6 with nothing being switched. So a face badge error can land at the same moment as the tread badge dropping, and the legs-gone mood is then lost on the badge. Read from Rocky's code, not tested: each legs event is sent to the face once, and a failed send is logged and dropped with no retry. The on-screen face window should still have shown it, but nobody was watching the window.

The scared and happy moods above were read from the face badge's state, not confirmed by eye. Pat's one remark was that Rocky "looks upset", which was his resting mood that day (angry 0.8, set before the tests). After the face badge came back on it reported battery 0; it had reported 100 before.

Switch-on delay: not measured yet. Pat could not see a clock during the run, and the test was skipped for now. The 16.3 s and 22.1 s above include the time the badge was left off, so they do not answer it. Once the badge was reachable again, the first move was accepted on the first try 1.7 to 2.0 s later.

## What is there today

Request | Answer today | Gap
Drive, move, pose, stop | {"ok": true} | No way to follow what became of it
GET /state, treads | reachable, driving, left, right, battery | These are the speeds asked for, not anything measured, and nothing says so
GET /state, sensors | distance_cm, touch, color, one shared age_ms | Each sensor has its own shape; no place for new ones; no source
The brain (rocky/body/sense.py) | Reads reachable, touch, distance_cm | Ignores the treads entirely

The path to the tread motors is one-way: infrared out, nothing back, and the LEGO motors have no sensors. So "the base moved" can only ever come from a separate sensor. This design makes that honest in the data.

## Decisions

| Decision | Why
D1 | Stay with JSON over the same endpoints. GET /state remains the one report. | It works and the brain already polls it.
D2 | Every drive move gets a number, and POST /drive returns it. | The brain can follow one move from start to end.
D3 | Every move ends with a stated result and reason. | "Not driving" alone cannot tell finished from stopped from lost.
D4 | The tread report holds only what was commanded. Anything measured lives under senses. | One place per fact; the brain never mistakes a wish for a reading.
D5 | Every sense has the same shape: value, source, age_ms. A value of null means "not known". | Pat, 6 October: "we need to unify it with some of the sensor readings at some point. So we need to stub that in."
D6 | Senses we expect but have not wired are listed now, with null values. | The shape is settled before the hardware arrives; filling one in later changes no interface.
D7 | The old top-level distance_cm, touch and color stay until the brain reads senses, then go. | Nothing breaks on the day this ships.
D8 | The report carries "schema": 2. | A reader can tell which shape it has.
D10 | The body service caps one move at 5 s ([drive] max_ms, adjustable up to the bridge's 10 s). | Added in the build. A longer drive is a chain of moves, each replacing the last.
D9 | The bridge, which runs the move, is the one that records how it ended. The body service passes that on and keeps no copy of its own. | Two records of the same ending would drift apart.
D11 | A face command that fails to reach the face badge is sent again: every 2 s for up to 10 s, and dropped as soon as a newer face is asked for, so a late "scared" cannot land on top of "happy". It covers every face send, not only legs moods. Both times are settings (badge_retry_every_s, badge_retry_for_s). | Pat, 7 October, after one of three legs-gone moods was lost to a face badge Bluetooth error: "sure retry".

## The life of a move

"Finished" means the bridge sent every command and the closing stop. It does not mean the base moved. Whether it moved is a question for senses.motion, which is empty until a sensor fills it.

A refused move was accepted by the bridge, numbered, and then turned down by the badge. Three things are not moves and get no number: a request outside the limits (422), a move for a badge that cannot be reached (503), and a move the badge was not ready for within start_within_ms (503). A move becomes lost as soon as anything, a status read included, finds the badge gone (C6).

## The new shape

POST /drive  {"left": 4, "right": 4, "ms": 1500}
→ 200 {"ok": true, "move": {"id": 17}}
→ 409 {"error": "the badge is low on memory", "move": {"id": 17}}   // refused by the badge
→ 503 {"error": "treads unreachable"}                               // not a move, no number
→ 422 {"detail": "ms must be from 100 to 5000"}                     // not a move, no number

GET /state
{
  "schema": 2,
  "reachable": true,                       // the arm's controller, as today
  "controller": "nxt",
  "joints": { "pan": {"deg": 12.0, "state": "moving"} },

  "drive": {
    "kind": "badge", "target": "tread", "reachable": true,
    "commanded": { "left": 4.0, "right": 4.0, "ms_left": 800 },
    "last_move": {
      "id": 17,
      "asked":  { "left": 4.0, "right": 4.0, "ms": 1500 },
      "result": "running",                 // running | finished | replaced | stopped | lost | refused
      "ended_by": null,                    // time | new_move | stop | unreachable | <refusal reason>
      "age_ms": 700                        // since it started, or since it ended
    },
    "recent_moves": [ { "id": 17, ... }, { "id": 16, "result": "replaced", "ended_by": "new_move", ... } ]
                                           // newest first, at most 8; the first is last_move
  },

  "senses": {
    "distance_cm": { "value": 42,            "source": "nxt.ultrasonic", "age_ms": 180 },
    "touch":       { "value": [false, true], "source": "nxt.touch",      "age_ms": 180 },
    "color":       { "value": "red",         "source": "nxt.color",      "age_ms": 180 },
    "tread_battery_pct": { "value": 100,     "source": "badge.tread",    "age_ms": 250 },

    "motion":      { "value": null, "source": null, "age_ms": null },   // still | moving | turning
    "heading_deg": { "value": null, "source": null, "age_ms": null },
    "tilt_deg":    { "value": null, "source": null, "age_ms": null },
    "bumped":      { "value": null, "source": null, "age_ms": null }
  },

  "distance_cm": 42, "touch": [false, true], "color": "red", "age_ms": 180   // old keys, kept for now (D7)
}

### Rules a reader can rely on

- A sense is always an object with value, source and age_ms. value: null means not known; never guess from it.
- New senses may appear at any time. A reader ignores names it does not know.
- drive.commanded is zero whenever no move is running.
- last_move is null until the first move after the service starts. Move numbers count up from 1 and start again when the bridge restarts; age_ms tells an old move from a new one.
- recent_moves and last_move are the bridge's own record, so they are still reported while drive.reachable is false.
- When drive.reachable turns false, a move that was running is already lost in that same report.
- A status read or a mood for a badge that is away is answered at once, never after a connect (C2, C8, C9). The slowest "it has just gone" answer is one Bluetooth deadline, 3 s.
- Right after the bridge restarts, a badge may read as unreachable for a few seconds until its first connect. A reader treats how it first finds a badge as no news.
- The first move after the badge comes back may be turned away as not ready (a connect takes about 2.6 s, the wait is 1 s). It gets no number; send it again.
- With no [drive] section, drive is null, as today.

## Where each piece lives

Project | Change
Mood bridge | The move task records its number, what was asked, and how it ended. POST /drive returns the number; GET /drive and DELETE /drive include last_move and recent_moves. The number is the bridge's own counter per badge. Bluetooth deadlines, the memory of a badge that is gone, and start_within_ms live here too (C1, C2, C5, C6).
Body service | POST /drive passes the number back. /state builds drive.commanded, drive.last_move and the senses block; a refusal it makes itself (limits) is not a move and gets no number. It sends start_within_ms with every move and answers 409 when the badge refuses one.
Rocky's brain | body.drive() returns the move number. BodySense reads senses in place of the old keys. Since 7 October (rocky/body/legs.py) it also reads drive.reachable and drive.recent_moves on each poll and tells Rocky, once each, of legs gone, legs back, and a move newly lost or refused. Rocky calls them his legs.
Badge firmware | None in this design.

## Stages

Stage | What | Needs
1 | Move numbers and endings, in the bridge and the body service. | Tests on the Mac; then two scripts for Pat to run on the Pi
2 | The senses block with today's sensors and the empty slots; the brain switches to it; old keys removed. | Tests on the Mac; Pi script
Later | Fill motion and tilt_deg from the badge's motion sensor (firmware, bridge). Fill bumped from an NXT touch sensor used as a bumper. Each is its own small design. | Hardware

## Testing

- Bridge, against a pretend badge: a move that runs out ends finished/time; one replaced ends replaced/new_move and the new one has the next number; one cancelled ends stopped/stop; a badge that drops ends lost/unreachable; a stop with nothing running changes nothing.
- Body service, against a pretend bridge: the number comes back from POST /drive; /state has the new shape with and without treads, with the arm unreachable, and with the bridge down; every sense has the three fields; the empty slots are present and null; old keys still match.
- Brain: BodySense reacts to touch and nearness from senses exactly as before.
- On the real base, with Pat: one move run to its end, one stopped, one replaced, and the badge switched off mid-move, checking each reported ending. Done: the first three on 6 October, the switch-off on 7 October (results above).
- Added in the build, bridge: a badge whose link goes half-open does not hang the bridge; a badge known to be gone answers at once; a move is lost as soon as a status read finds the badge gone; a move does not start after start_within_ms; a refused move is numbered and ends refused.

## Open points

- A legs mood is lost if the face badge has a Bluetooth error at that moment. Seen once in three switch-offs on 7 October. Rocky sends each legs mood once and drops it if the send fails. Decided (D11): retry it. Built in rocky-robot on 7 October and tested against a pretend badge; not committed, not yet running in Rocky (his brain needs a restart), and not tried on the base.
- The face moods for legs gone and back have not been confirmed by eye. They were read from the face badge's state. Rocky's brain reacted to each lost move in the same report that showed it.
- The switch-on delay is still unmeasured. Skipped on 7 October. To measure it: time from the badge's menu appearing to the treads moving.
- A move sent just as the badge drops took 2.05 s to be turned away. It was in flight before anything knew the badge was gone, so it is not the "known gone" case, and it is inside the 3 s deadline. What made up the 2.05 s is not known; the Pi's log for 22:42:36 to 22:42:39 BST on 7 October would show it.
- The arm is still the pretend controller on the Pi, by intent: that build phase has not started. Its joints report "needs home" after every service restart and its touch and distance values are not real.
- Mood sequences do not have the short cut in C9. A sequence for a badge that is away still waits on a connect at each step.
- A badge with its own Drive app open still ignores commands silently, so such a move would be reported finished. Fixing that needs a status flag from the firmware; when it exists the ending becomes refused.
- The arm's poses deserve the same treatment (a number and an ending per pose). Left out here to keep this small.
- /state asks the bridge each time, so a hung bridge can slow the whole report by up to two seconds. Worth caching the tread part if it bites.
- Battery reads 0 on the face badge. On 7 October it read 100 until the badge was switched off and on, then 0. It will show as 0, not null, until the firmware reports it properly.
