pjerus/Temporal-Replay-26-Badge/docs/superpowers/specs/rocky-pi-tread-drive-design.html

# Driving the treads from rocky-pi

Started 2026-10-06 · Revision 3 (2026-10-06) — stages 2 and 3 passed: the tank drives from the Mac through rocky-pi (see "Results on hardware") · status: working on rocky-pi; stage 4 and the follow-ups remain · follows on from Tread drive over Bluetooth (its decision D7)

## In one paragraph

Rocky's brain asks the body service on rocky-pi to drive: a left speed, a right speed and a length of time. The body service hands that to a small drive driver. Today's driver passes it to the mood bridge, which already holds the Bluetooth link to each badge, and the badge turns it into infrared for the LEGO receiver. Which badge drives is one setting. A different kind of motor hardware later means a new driver, not a new way of asking.

## What we are building on

Fact | How we know
Both badges accept drive commands over Bluetooth and stop when commands stop | Driven from the Mac on carpet, 6 October; firmware commit b83064a
The mood bridge runs on rocky-pi (port 8026) and keeps one open Bluetooth link per badge | Read in pi-arduino-face-emotions: bridge.py, backends.py
The bridge already handles several badges, each with an address and a secret | EMOTION_BADGES setting in config.py
A badge takes one Bluetooth connection at a time | Firmware design; whoever holds the link must carry every kind of message
The body service has a key-protected web endpoint, a stop command and a state report, and the brain has a client for it | Read in rocky-robot: body/service/app.py, rocky/body/client.py
The drive service uses the same 8-character secret as the mood service | Firmware: one secret passed to both

not yet proven The body service has never run on rocky-pi (yesterday's hardware bring-up is still pending), and rocky-pi has never held three Bluetooth links at once (two badges and the NXT brick).

## How a drive command travels

## Decisions

| Decision | Why
D1 | The mood bridge carries drive commands, for any badge it knows. | It already owns the one Bluetooth link each badge allows. The face badge can then show moods and drive on the same link.
D2 | The body service gets a general POST /drive, with a swappable driver behind it. | Pat, 6 October: "we're gonna need that kind of control when we get the driver boards or whatever other solution we come up with". The brain asks the same way whatever moves the treads.
D3 | Which badge drives is a setting in the body service (the bridge's name for that badge). | Pat chose "either, chosen by a setting".
D4 | The bridge does the fast resending; the body service sends one request per move. | The badge needs a fresh command about every 0.2 s. The bridge sits next to the Bluetooth link, so Wi-Fi hiccups between the Mac and the Pi cannot starve it.
D5 | Every move has a length, capped at 5 seconds (a setting). A longer drive is several moves. | A brain that goes quiet cannot leave the base running.
D6 | The body service's existing /stop also stops the treads, and a new move replaces the one running. | One stop for the whole body; a stop always wins.
D7 | Driving does not depend on the NXT brick. If the brick is unreachable the treads still work, and the reverse. | They are separate hardware; one failing should not take the other down.
D8 | The brain gets a drive call on its body client and nothing more for now. Teaching Rocky when to drive is a later design. | Keeps this piece small and testable.
D9 | No firmware change. | The badges already do everything this needs.

### Approaches considered

Approach | Verdict
Bridge carries drive, body service fronts it (chosen) | Works for either badge; one more local hop; two projects change.
Body service opens its own Bluetooth link to the badge | Fine for the spare, impossible for the face badge while the bridge holds its link. Fails "either".
Brain calls the bridge directly, no body service | Fewer parts, but the brain would then be tied to badges, which is what D2 avoids.

## Part 1: the mood bridge (pi-arduino-face-emotions)

Endpoint | Body | Does
POST /drive | target, left, right (−7 to 7, one decimal), ms (100 to 10000) | Starts a background task that sends the command every 0.2 s with a 0.6 s lifetime until ms is up, then sends a stop. Answers at once. Replaces any move already running for that badge. Both speeds 0 means stop.
DELETE /drive?target= | | Cancels the running move and sends a stop.
GET /drive?target= | | Reads the badge's 8-byte drive status: driving, infrared ready, low memory, rejected, speeds, time left, battery, free memory.

- Same key check, same per-badge lock and same error answer (502 when the badge is out of reach) as the mood endpoints.
- The 11-byte command and 8-byte status are built and read by small pure functions, copied in meaning from pf_ble_drive.py and tested without Bluetooth.
- The three drive addresses (UUIDs) join the mood ones in config.py, each overridable by an environment variable.
- A badge whose firmware has no drive service answers 502 with a plain message; moods on it are unaffected.
- The move task ends quietly if the badge drops out; the badge stops by itself within 0.6 s.

## Part 2: the body service (rocky-robot)

# ~/.config/rocky-body/settings.toml on rocky-pi
[drive]
kind = "badge"                      # "badge", "fake", or leave the section out for no treads
bridge_url = "http://127.0.0.1:8026"
target = "tread"                    # the bridge's name for the badge that drives
max_ms = 5000
max_speed = 7.0

The bridge's key comes from the environment (ROCKY_DRIVE_BRIDGE_KEY), never from the settings file.

Piece | What it does
body/service/drive.py | The driver shape (drive(left, right, ms), stop(), state()), a BadgeDrive that calls the bridge, and a FakeDrive for tests and for running without hardware.
settings.py | Reads and checks the [drive] section.
app.py | POST /drive; /stop stops treads as well as joints; /state gains a drive part. No [drive] section means /drive answers 404 "this body has no treads".
rocky/body/client.py | await body.drive(left, right, ms).

### Worked example

# forward at speed 4 for one and a half seconds (about a foot on carpet)
POST http://rocky-pi.local:8027/drive
Authorization: Bearer <body key>
{"left": 4, "right": 4, "ms": 1500}
→ 200 {"ok": true}

# quarter turn to the right
{"left": 4, "right": -4, "ms": 500}

# what the state report adds
GET /state → { ..., "drive": {"kind": "badge", "target": "tread", "reachable": true,
                               "driving": false, "left": 0, "right": 0, "battery_pct": 0} }

Asked for | Answer
Speed beyond max_speed, ms beyond max_ms, or not a number | 422, nothing sent
Badge or bridge out of reach | 503 "treads unreachable"
Badge refused (low memory, or a command it rejected) | 409 with the reason; the body service also tells the bridge to stop resending
No [drive] section | 404

## What stops the base

If this goes wrong | The base stops because | Within
The brain goes quiet mid-move | Every move has an end; the bridge sends a stop then | the move's own length, at most 5 s
The body service crashes | Same: the bridge finishes the move and stops | at most 5 s
The bridge crashes or the Pi loses power | The badge's command lifetime runs out | 0.6 s
Bluetooth drops | The badge stops on disconnect | at once
The badge dies or is blocked from the receiver | The LEGO receiver's own timeout | about 1 s
Anyone calls /stop | The move is cancelled and a stop is sent | about 0.1 s

## Security

- Both endpoints keep their existing key checks. The body service's port is open to the home network, as it is today; the bridge is also reachable on the home network with its own key (the brain already uses it for moods), so it keeps its own limits: speed 7 and 10 seconds a move.
- This adds a way to make a physical thing move from the network, so the limits (speed, length) are enforced in the body service, not trusted from the caller.
- known gap The badge's 8-character secret is fixed in the firmware source and sent unencrypted over Bluetooth. It now guards motion. Fixing it (a per-badge secret and an encrypted link) is a separate piece of work and is not part of this design.

## Corrections from the build

Revision 1 said | What is true
A badge with its own Drive app open answers "refused" | It ignores Bluetooth commands silently. The body service answers success while the base stays still. Reporting it needs a firmware change (a status flag).
A refusal is reported on the command that caused it | It can arrive one command late: the badge handles a command a moment after the bridge reads its status.
The state report always answers quickly | It asks the bridge each time, so a hung bridge can cost up to 2 seconds.
/stop stops joints and treads | It does attempt both, always. But if one side is unreachable the answer is an error, and it does not say that the other side did stop.

Stage 1 lives on branch tread-drive in both projects: the mood bridge at 24eff40, rocky-robot at 642dbf1. Not pushed. rocky-robot's own copy of the bridge package (rocky/badge/emotion_channel/) was not updated; the new driver does not use it.

## Results on hardware (6 October)

Stage | Result
2. Whole chain on the Mac | passed Forward, early stop and move-replaced-by-spin all seen by Pat on the real base with the spare badge.
3. On rocky-pi | passed Bridge updated and now holds two badges: badge (the face) and tread (the spare). Body service installed as rocky-body on port 8027 with a pretend arm and real treads. The same three moves, sent from the Mac, seen by Pat. A command takes about 0.25 to 0.35 s from the Mac to an answer.
4. Three links at once | not run Two badge links held together without trouble; the NXT brick was not connected.

- Restarting the bridge left the face badge's link stuck. Requests for it hung until the badge was switched off and on. The bridge should drop its links cleanly on shutdown, or time out a hung read.
- rocky-pi's address changed to 192.168.86.55 after a restart; the name rocky-pi.local still works.
- Rocky's brain does not have the body service's key yet. It was created on the Pi; the notes say it also belongs in the Mac Keychain item rocky-pi-body.
- Old bridge code and settings are kept on the Pi as src.bak-2026-10-06 and env.bak-2026-10-06.

## Testing

Stage | What | Needs Pat
1 | Unit tests on the Mac: command and status functions; bridge endpoints against a pretend badge (resend pacing, replace, cancel, stop at the end, badge dropping out); body service against a pretend bridge (limits, errors, stop, state); the brain's client. | No
2 | The whole chain on the Mac: bridge and body service both running here, real badge, treads off the desk, then on carpet. | Yes, watching
3 | On rocky-pi: update the bridge, install the body service, add the spare to the bridge's badge list, drive from the Mac through the Pi. | Yes; changes a running service on the Pi
4 | Three links at once: face badge showing moods, spare driving, NXT brick connected. Ten minutes. | Yes

## Open points

- Each badge's Bluetooth address as rocky-pi sees it. Found by a scan on the Pi at stage 3; it is not the same as the USB hardware address.
- Battery percent reads 0 in the badge's drive status. Reported as-is for now.
- The face badge as the driver needs its top edge to see the receiver. A mounting question, not a software one.
- Named moves ("forward a foot", "quarter turn left"), like the arm's named poses, would suit Rocky's brain. Left for the design that teaches Rocky when to drive.
