pjerus/Temporal-Replay-26-Badge/docs/superpowers/specs/tread-drive-ble-design.html

# Tread drive over Bluetooth

Started 2026-10-06 · Revision 2 (2026-10-06) — Pat settled the three open points (D7 to D9) · status: approved, ready for the build plan

## In one paragraph

The spare badge rides on the tank base with no cable. A computer (the Mac for testing, later rocky-pi) sends it a small Bluetooth message: a speed for the left tread and a speed for the right. The badge turns that into the LEGO infrared signal the base already obeys. If the messages stop for any reason, the base stops. This first version covers the two treads only; motor boards on the I2C port are a later step.

## What is already proven

Fact | How we know
The badge drives both treads by infrared, with seven speed steps each | Driven from the Mac over USB, 6 October
Left tread is output A, right is output B, and the right side is reversed | One-at-a-time tests with Pat watching
The left tread needs to run 9% faster to go straight | Carpet, no load, speed 4
The LEGO receiver stops the motors when signals stop | Seen on every test
Bluetooth and send-only infrared run together on one badge | echo-drive build; Pat saw the base move

## How the pieces connect

## Memory: where it goes and how we avoid running out

The chip has two kinds of memory. The large external memory (8 MB) holds the Python runtime and is not the problem. The small internal memory is what Bluetooth and infrared must use, and that is the tight one. The bars below show the internal memory left over after the rest of the firmware has started, which is about 102 KB.

Figure | Value | Status
Internal memory free before infrared starts, no Bluetooth | 101.6 KB | measured
Same, with Bluetooth running | 19.7 KB | measured
Free with Bluetooth and the infrared sender both running | 9.3 KB, largest single piece 7.2 KB | measured
Infrared receiver's share | about 14 KB | measured (I said 25 KB earlier; the log shows 14)
Extra memory used while a controller is connected | not known | not measured
Extra memory the new drive service needs | target under 1 KB | design target

### The rules that keep us inside the edge

1. Nothing new is created while driving. The drive service sets up everything it needs once at start-up and reuses it. No new background task, no growing lists.
2. The badge reports its own free memory. The status it sends back includes the free amount now and the lowest it has ever been since power-on. The controller can see trouble coming.
3. A floor of 6 KB. If free memory is below 6 KB when a controller asks to drive, the badge refuses, stays stopped, and says so in its status.
4. Measure first. The first build step is to connect a controller and read those two numbers. If connecting alone drops free memory under the floor, the build stops there and I free memory before going on (the candidates are the Wi-Fi start-up attempt and the oversized main stack).
5. Pass mark: ten minutes of driving with the lowest-ever figure still above 6 KB.

Each figure comes from a single start-up, so treat them as good to a kilobyte or two. The one unknown that matters is the cost of a live connection, and rule 4 settles it before anything else is built.

## The Bluetooth messages

A second small service sits beside the existing mood service, with the same shape: one place to write commands, one place to read status. It uses the same 8-byte shared secret the mood service uses, so only your own controller can drive.

### Drive command (11 bytes, written by the controller)

Bytes | Meaning | Range
0–7 | Shared secret | must match, or the message is ignored
8 | Left tread speed, in tenths | −70 to 70 (so 43 means speed 4.3); positive is forward
9 | Right tread speed, in tenths | −70 to 70
10 | How long this command stays valid, in tenths of a second | 1 to 10 (one second at most)

The controller repeats the command about five times a second while it wants the base to move. Speeds of 0 and 0 mean stop now. Anything out of range is ignored and the base is left as it was.

### Status (8 bytes, read by the controller)

Byte | Meaning
0 | Flags: driving now · infrared ready · refused for low memory · last command rejected
1, 2 | Left and right speed currently being sent, in tenths
3 | Time left on the current command, tenths of a second
4 | Battery percent
5 | Free internal memory now, in quarter-kilobytes (36 means 9 KB)
6 | Lowest free internal memory since power-on, same unit
7 | Count of commands accepted, wrapping at 255

## Stopping: the safety rule

Same rule as the brick body: a stop always wins, and silence means stop. There are three layers, each catching what the one before it misses.

## What gets built

Piece | Where | Job
Tread signal maker | firmware/src/drive/PfTreads.h/.cpp | Turns left and right speeds into LEGO infrared frames: trim, right-side flip, in-between speeds. A straight port of the tuned ir_drive.py; no hardware calls, so it is tested on the Mac.
Drive service | firmware/src/drive/DriveBleService.h/.cpp | The Bluetooth command and status, the timer, the stop rules, the memory floor.
Hook-up | firmware/src/main.cpp | Start the service after the mood service; call its tick from the main loop.
Settings | firmware/settings.txt (via BadgeConfig) | Bluetooth name, LEGO channel, left trim, right flip, transmit power. Each has a default equal to today's tuned value.
Build variant | [env:echo-drive] | Gains -DBADGE_ENABLE_DRIVE_BLE. Other builds, including the face badge's, are unchanged.
Test controller | firmware/scripts/pf_ir/pf_ble_drive.py | Mac-side script: same arguments as pf_drive.py, but over Bluetooth, and it prints the memory figures.

### Worked example

pf_ble_drive.py 4 4 1500        # forward about a foot
  → writes  [secret] 28 28 0A   five times a second for 1.5 s   (0x28 = 40 tenths)
  → badge sends left 4.36 (trim applied), right 4, as infrared every 90 ms
  → after 1.5 s the script writes  [secret] 00 00 01  and reads status:
     driving=no  battery=98%  free=8.5 KB  lowest=8.0 KB

## Decisions

# | Decision | Why

D1 | Drive logic lives in the firmware, not a Python app | Pat, 6 Oct. Works from power-on; stop rule enforced in one place.
D2 | First version is treads only | Pat, 6 Oct. I2C motor boards cannot be tested until they arrive.
D3 | Infrared is send-only on this build | The receiver does not fit beside Bluetooth (see the memory bars).
D4 | Tuning values are settings, not constants in the code | They change with load and floor; re-tuning should not need a rebuild.
D5 | A separate Bluetooth service, not extra fields on the mood service | The face badge's mood protocol stays untouched; the two can be told apart.
D6 | Infrared comes up when a controller connects and goes down when it leaves | Gives back 10 KB whenever nobody is driving.
D7 | Prove it from the Mac first; rocky-pi integration follows afterwards | Pat, 6 Oct. The Pi holding two badges plus the brick at once is unproven and deserves its own test.
D8 | On the drive build the badge announces itself over Bluetooth as "Rocky IR Tread" | Pat, 6 Oct. Never confused with the face badge. The name is a setting with that default.
D9 | The screen shows one plain status line and nothing more | Pat, 6 Oct.

## How it will be tested

1. On the Mac, no hardware: the signal maker produces the same frames as the tuned Python script for a table of speeds, including in-between ones.
2. Badge on USB: connect by Bluetooth, read the memory figures (rule 4).
3. Cable unplugged, base on the carpet: forward, back, both spins, and a quarter turn, matching today's results.
4. Stop layers: kill the script mid-move (layer 1), switch the Mac's Bluetooth off mid-move (layer 2), cover the badge's emitter mid-move (layer 3). The base must stop each time within about a second.
5. Ten minutes of mixed driving; lowest free memory stays above 6 KB.

## Not in this version

- Motor boards on the I2C port.
- rocky-pi and the brain driving the base (follow-on, see D7).
- Listening to the LEGO handheld remote.
- Distances and angles ("forward 30 cm"). The base has no sensors, so those stay as timing on the controller side.
- Any change to the face badge or its firmware.
