pjerus/Temporal-Replay-26-Badge/docs/pocket-scanner/superpowers/specs/repo-consolidation-design.html

# Pocket Scanner: overview and repo consolidation

Started 2026-10-04 · Revision 2 (2026-10-04) · Status: done. Decisions settled, consolidation complete

Pocket Scanner is custom firmware for a Temporal Replay 26 conference badge, turning it into a handheld Bluetooth scanner. Today the work sits in two GitHub repos, and one of them (temporal-badge-scanner) only holds docs. This page describes the project and records the consolidation: the docs were folded into pjerus/Temporal-Replay-26-Badge and the docs-only repo was deleted.

## 1. What the project is

The badge is an ESP32-S3 handheld with a small OLED screen, an 8×8 LED matrix, a joystick, four buttons, a motion sensor, infrared send/receive, WiFi and Bluetooth LE. It has no speaker; the only “sound” is the vibration motor buzzing. Apps are small MicroPython programs stored on the badge’s file system; the core is C++ (Arduino framework, built with PlatformIO).

Phase | Scope | State
1 | Strip DOOM, conference menus and games; add a hardware-exercise demo (joystick, buttons, motion, OLED, LEDs) | done
2 | Bluetooth scan: C++ scanner exposed to MicroPython as badge.ble_scan_*; live device list sorted by signal strength | working
2 (extras) | leddemos (fire, plasma, matrix rain) and billboard (scrolling name tag) | shipped
3? | WiFi and IR scanning | not started

### Known loose ends

- Five Bluetooth names were hand-patched into a generated file, with a workaround in qstr.c. The proper fix is re-running setup_arduino_embed.sh.
- The factory-restore path in CLAUDE.md says ~/backups/...; the file is really at pi-arduino/backups/firmware-v0.2.4/.
- fixed The registry entry in ~/ai-dev/index.html said GitHub none and described Phase 2 as covering BLE, WiFi and IR. It was updated on 2026-10-04.

## 2. The repos before

## 3. Result: one repo

pjerus/Temporal-Replay-26-Badge is the single home. The docs now live under docs/pocket-scanner/ and temporal-badge-scanner is deleted.

### Decisions

# | Question | Decision | Status

D1 | Where do the docs live? | docs/pocket-scanner/ on pocket-scanner-phase2. Upstream’s own docs/ and CLAUDE.md are untouched, so merges from upstream stay clean. | settled
D2 | Fate of the old repo | Deleted pjerus/temporal-badge-scanner after the move was pushed and checked. | done
D3 | Other stale repos | None. The only other badge-related repo is the fork itself. | settled
D4 | History of the docs repo | Files copied as one fresh commit (a32524b); old history not carried over. | settled
D5 | Factory restore image | Stays local in pi-arduino/backups/. Not committed and not uploaded as a release asset. | settled
D6 | Fork default branch | Changed from upstream’s main to pocket-scanner-phase2, so visitors see our README. | done

### Steps taken

1. done Copied the docs into docs/pocket-scanner/ on pocket-scanner-phase2, fixed paths inside README.md and CLAUDE.md (older specs, plans and checkpoints still say upstream/firmware/...; read that as firmware/...), and rewrote the “two repos” intro.
2. done Committed and pushed to the fork; confirmed the files appear on GitHub.
3. done Checked links: neither pjerus.github.io nor the registry mentioned the old repo.
4. done Deleted pjerus/temporal-badge-scanner on GitHub (needed the delete_repo permission on gh).
5. done Set pocket-scanner-phase2 as the fork’s default branch.
6. done Local clean-up: removed the outer .git, the duplicate docs and the old .gitignore. temporal-badge-scanner/ now holds only upstream/; open sessions from there.
7. done Updated the registry entry.

## 4. Registry entry (as updated)

{ name: "pi-arduino (Pocket Scanner)", state: "on-hold",
  github: "pjerus/Temporal-Replay-26-Badge (public fork)",
  latest: "Phase 2 Bluetooth scan, LED demos and billboard work. Waiting on: WiFi and IR scanning (Phase 3)." }

“Waiting on” is a guess at the next step; correct it if Phase 3 isn’t the plan.

## 5. Hardware follow-ups (2026-10-04)

Questions raised after the consolidation. Nothing here is built or tested.

Idea | What we know | Status
Add a small speaker | The Echo board has no audio path; only the motor on GPIO6 buzzes. Options: a piezo buzzer on one free pin, an I²S amplifier with a small speaker (three pins plus new audio code), or a Qwiic buzzer if the board has the connector. | needs board check
Free pins | Pins 0–14, 17, 18, 21, 38 and 42 are used (EchoDefines.h). The repo has KiCad files for ALPHA, BRAVO and CHARLIE only, so we can’t tell which others reach a pad on Echo. badge-form-factor_R2.jpeg is a design sketch, not a photo. | open
Run Tailscale | No official ESP32 client. The community MicroLink (https://github.com/CamM2325/microlink) project targets ESP32-S3 (about 100 KB RAM, PSRAM recommended, ESP-IDF 5.0+). This firmware uses the Arduino framework, so integration is real work. Not reviewed or tested. | possible, unvetted
Pin table in CLAUDE.md | Was copied from upstream’s older docs and was wrong for Echo. Corrected from EchoDefines.h. | fixed

### Speaker and microphone parts, with prices

US list prices as of 2026-10-04, taken from retailer search results. Before shipping and tax; not re-checked on each product page.

Part | Use | Price | Where
Piezo buzzer PS1240 (Adafruit 160) | Beeps on one GPIO | $0.95 to $1.99 | Pi Shop $0.95, Tinkersphere $1.49, Jameco $1.99
I²S amp, MAX98357A (Adafruit 3006) | Real audio, three GPIOs | $5.95 | Adafruit
Mini metal speaker 8 Ω 0.5 W (Adafruit 1890) | Pairs with the amp | $1.95 | Adafruit (out of stock when checked); Micro Center $2.99
SparkFun Qwiic Buzzer (BOB-24474) | Beeps over I²C, needs a Qwiic port | $10.50 | SparkFun
Generic INMP441 I²S mic module | Microphone, shares clock pins with the amp | $2.99 to $4.95 | EasyElecModule $2.99, ElectroPeak $3.87, Vetco $4.95 (Tayda $1.59, out of stock); quality varies
Adafruit I²S MEMS mic, SPH0645LM4H (Adafruit 3421) | Microphone | $6.95 to $9.15 | Micro Center $6.95, Jameco $9.15
Adafruit I²S MEMS mic, ICS-43434 (Adafruit 6049) | Microphone | $8.95 | Adafruit

Rough totals: buzzer about $1 to $2; amp plus speaker about $8 to $9. Adding a mic brings speaker plus mic to about $11 to $18. A mic and amp can share the two clock pins, so about four free pins cover both.

## 6. In plain terms

Before, the badge code lived in one GitHub repo and the notes about it in another. The notes now sit next to the code and the notes-only repo is gone.
