pjerus/Temporal-Replay-26-Badge/specs/006-openapi-badge-api/data-model.md

# Data Model: BadgeAPI_types.h

All types defined here are generated by `scripts/gen_badge_api_types.py` from
`specs/openapi.json`. **Do not edit `BadgeAPI_types.h` by hand.**

---

## Size Constants

```c
// Defined at the top of BadgeAPI_types.h
#define BADGE_FIELD_NAME_MAX      64   // name, title, company, partner_name, etc.
#define BADGE_FIELD_TYPE_MAX      16   // attendee_type: "Attendee", "Staff", etc.
#define BADGE_UUID_MAX            37   // UUID v4: 36 chars + null terminator
#define BADGE_WORKFLOW_ID_MAX     96   // "badge-pairing-<uuid>-<uuid>" + margin
#define BADGE_PING_ACTIVITY_MAX   32   // activity_type stream name
#define BADGE_PING_DATA_MAX      256   // raw JSON payload char buffer
#define BADGE_PING_CURSOR_MAX    128   // base64 keyset cursor
#define BADGE_PING_TIMESTAMP_MAX  32   // ISO 8601: "2026-03-13T00:00:00.000Z"
#define BADGE_PINGS_MAX_RECORDS    8   // fixed-capacity page size for GetPingsResult
```

---

## Base Result Struct

```c
// All API result structs begin with these two fields.
// ok == false: all other fields are zero/empty.
// ok == true:  all fields are valid.
typedef struct {
    bool ok;        // false on network error, non-2xx, or parse failure
    int  httpCode;  // raw HTTP response code; 0 if connection failed
} BadgeAPIResult;
```

---

## Status Enum

```c
typedef enum {
    BOOP_STATUS_UNKNOWN       = 0,  // parse failure or unrecognized value
    BOOP_STATUS_PENDING       = 1,  // workflow running; poll again
    BOOP_STATUS_CONFIRMED     = 2,  // mutual consent complete
    BOOP_STATUS_NOT_REQUESTED = 3   // expired, cancelled, or never started
} BadgeBoopStatus;
```

---

## Structs (generated from OpenAPI schemas)

### BadgeInfoResult
*Used by: `getBadgeInfo`, `fetchBadgeXBM`*
*OpenAPI schema: `BadgeInfoResponse` (`/api/v1/badge/{id}/info`)*

```c
typedef struct {
    bool ok;
    int  httpCode;
    char name[BADGE_FIELD_NAME_MAX];
    char title[BADGE_FIELD_NAME_MAX];
    char company[BADGE_FIELD_NAME_MAX];
    char attendee_type[BADGE_FIELD_TYPE_MAX];
} BadgeInfoResult;
```

### FetchQRResult
*Used by: `getQRBitmap`*
*Endpoint: `GET /api/v1/badge/{id}/qr.xbm` — binary XBM response*

```c
typedef struct {
    bool     ok;
    int      httpCode;
    uint8_t* buf;    // heap-allocated XBM bytes; caller must free()
    int      len;    // byte count; 0 on failure
} FetchQRResult;
```

Note: `FetchQRResult` retains heap allocation because XBM bitmaps are 1,024 bytes —
too large for stack allocation on an 8 KB task stack.

### FetchBadgeXBMResult
*Used by: `fetchBadgeXBM`*
*Endpoint: `GET /api/v1/badge/{id}/info` — bitmap + role parsed from JSON*

```c
typedef struct {
    bool     ok;
    int      httpCode;
    uint8_t* buf;          // heap-allocated bitmap bytes; caller must free()
    int      len;
    int      assignedRole; // ROLE_NUM_* constant from BadgeConfig.h
} FetchBadgeXBMResult;
```

### BoopResult
*Used by: `createBoop`*
*OpenAPI schemas: `PairingPendingResponse` (202), `PairingConfirmedResponse` (200)*

```c
typedef struct {
    bool           ok;
    int            httpCode;
    BadgeBoopStatus status;
    char           workflowId[BADGE_WORKFLOW_ID_MAX];   // non-empty when status==PENDING
    int            pairingId;                           // non-zero when status==CONFIRMED
    char           partnerName[BADGE_FIELD_NAME_MAX];
    char           partnerTitle[BADGE_FIELD_NAME_MAX];
    char           partnerCompany[BADGE_FIELD_NAME_MAX];
    char           partnerAttendeeType[BADGE_FIELD_TYPE_MAX];
} BoopResult;
```

### BoopStatusResult
*Used by: `getBoopStatus`*
*OpenAPI schema: `PairingStatusResponse` (`/api/v1/boops/status/{workflow_id}`)*

```c
typedef struct {
    bool           ok;
    int            httpCode;
    BadgeBoopStatus status;
    char           workflowId[BADGE_WORKFLOW_ID_MAX];   // present when status==PENDING
    int            pairingId;                           // present when status==CONFIRMED
    char           partnerName[BADGE_FIELD_NAME_MAX];
    char           partnerTitle[BADGE_FIELD_NAME_MAX];
    char           partnerCompany[BADGE_FIELD_NAME_MAX];
    char           partnerAttendeeType[BADGE_FIELD_TYPE_MAX];
} BoopStatusResult;
```

### BoopPartnerResult
*Used by: `getBoopPartner`*
*OpenAPI schema: `PartnerInfoResponse` (`/api/v1/boops/{id}/partner`)*

```c
typedef struct {
    bool ok;
    int  httpCode;
    int  pairingId;
    char partnerName[BADGE_FIELD_NAME_MAX];
    char partnerTitle[BADGE_FIELD_NAME_MAX];
    char partnerCompany[BADGE_FIELD_NAME_MAX];
    char partnerAttendeeType[BADGE_FIELD_TYPE_MAX];
} BoopPartnerResult;
```

### PingRecord
*Used by: `sendPing`, inner record for `GetPingsResult`*
*OpenAPI schema: `PingRecord` (`/api/v1/pings` POST response and GET list element)*

```c
typedef struct {
    char id[BADGE_UUID_MAX];
    char source_ticket_uuid[BADGE_UUID_MAX];
    char target_ticket_uuid[BADGE_UUID_MAX];
    char activity_type[BADGE_PING_ACTIVITY_MAX];
    char data[BADGE_PING_DATA_MAX];         // raw JSON object, null-terminated
    char created_at[BADGE_PING_TIMESTAMP_MAX];
    char updated_at[BADGE_PING_TIMESTAMP_MAX];
} PingRecord;
```

### SendPingResult
*Used by: `sendPing`*
*Endpoint: `POST /api/v1/pings`*

```c
typedef struct {
    bool       ok;
    int        httpCode;
    PingRecord record;    // populated on ok==true
} SendPingResult;
```

### GetPingsResult
*Used by: `getPings`*
*OpenAPI schema: `PingListResponse` (`/api/v1/pings` GET)*

```c
typedef struct {
    bool       ok;
    int        httpCode;
    PingRecord records[BADGE_PINGS_MAX_RECORDS];
    int        count;                          // actual records in this page
    char       next_cursor[BADGE_PING_CURSOR_MAX]; // empty string if no further pages
} GetPingsResult;
```

### ProbeResult
*Used by: `probeBadgeExistence`*
*Endpoint: `GET /api/v1/badge/{id}/info` — status-only probe, fields not parsed*

```c
typedef struct {
    bool ok;        // true if HTTP 200; false otherwise
    int  httpCode;
} ProbeResult;
```

---

## Entity Relationships

```
openapi.json
    ↓ gen_badge_api_types.py
BadgeAPI_types.h          ← included by BadgeAPI.h
    ↑                       ← included by all firmware modules
BadgeAPI.h
BadgeAPI.cpp               ← implements all BadgeAPI:: functions
    ↑ calls
BadgePairing.cpp           ← probeBadgeExistence() replaces inline HTTPClient
BadgeIR.cpp (irTask)       ← createBoop, getBoopStatus, cancelBoop
```

---

## State Transitions

`BoopStatus` drives the pairing state machine in `BadgeIR`:

```
UNKNOWN (parse error — retry)
PENDING ──── poll getBoopStatus ──── CONFIRMED → enter PAIRED state
         └── timeout / button ────── NOT_REQUESTED → reset to IDLE
```

`ProbeResult` drives the badge activation polling in `osUnpairedFlow`:

```
ok=false, httpCode=-1   → "conn err" display status
ok=false, httpCode=404  → "HTTP 404" display status (badge not yet registered)
ok=true,  httpCode=200  → trigger fetchBadgeXBM → enter PAIRED state
```

---

## Validation Rules

- All char arrays are null-terminated and truncated to their declared size minus 1.
- On `ok == false`, all fields beyond `ok` and `httpCode` are zero-initialized.
- `pairingId == 0` means "not set" (backend IDs start at 1).
- `PingRecord.data` truncation: if the backend JSON exceeds `BADGE_PING_DATA_MAX - 1`
  bytes, the buffer is filled to capacity and null-terminated. No byte-count field is
  needed because apps using pings should design their `data` payloads to fit; the firmware
  is a passthrough, not a JSON processor.
- `GetPingsResult.count > BADGE_PINGS_MAX_RECORDS` cannot occur — excess backend records
  are silently discarded. Use `next_cursor` to page.
