pjerus/Temporal-Replay-26-Badge/specs/007-embed-micropython-runtime/plan.md

# Implementation Plan: Embed MicroPython Scripting Runtime

**Branch**: `007-embed-micropython-runtime` | **Date**: 2026-03-16 | **Spec**: [spec.md](spec.md)
**Input**: Feature specification from `/specs/007-embed-micropython-runtime/spec.md`

---

## Summary

Embed MicroPython v1.27.0 as a scripting runtime inside the Arduino C++ firmware (Firmware-0308-modular). The C++ firmware remains the host OS. MicroPython is initialized once during the boot sequence (WiFi connection window), runs inline in `loop()` on Core 1 when a Python app is selected from the menu, and is soft-reset between app launches.

The runtime exposes a single `badge` C extension module covering display (namespaced sub-object), button input, IR send/receive, WiFi/HTTP, GPIO/ADC, GC control, and app exit. Apps are plain `.py` files on the badge VFS. No existing firmware behavior changes.

---

## Technical Context

**Language/Version**: Arduino C++ (ESP32 Arduino core 3.x) + MicroPython v1.27.0 embed port
**Primary Dependencies**: MicroPython `ports/embed` (generated C sources); existing libraries unchanged
**Storage**: Badge VFS (FAT); apps as `/apps/<name>.py`; `micropython_embed/` generated by `setup.sh` (gitignored)
**Testing**: Manual verification per spec's acceptance scenarios; build verification via `./build.sh`
**Target Platform**: ESP32-S3-MINI-1, XIAO form factor; Arduino ESP32 core 3.x on ESP-IDF 5.x
**Project Type**: Embedded firmware — scripting runtime component
**Performance Goals**: GC pause ≤ 20ms; app load ≤ 2s from menu select; emergency escape ≤ 1s
**Constraints**: ≤ 128 KiB DRAM for MicroPython heap; Core 1 only; no FreeRTOS task for VM; no `machine`/`esp32` modules
**Scale/Scope**: Single badge; ~10 apps; interpreter runs one app at a time; soft-reset between launches

---

## Constitution Check

*All seven principles reviewed. All pass.*

| Principle | Status | Notes |
|---|---|---|
| **I. Arduino C++ First** | ✅ Pass | Constitution v2.4.0 explicitly permits the embedded MicroPython scripting surface under Principle I's permitted exception clause (spec 007). All four constraints satisfied: VM runs on Core 1 inline in `loop()`, hardware ownership stays in C++, `badge` module is sole crossing point, no existing firmware behavior depends on the scripting runtime. |
| **II. Firmware-0308 as Behavioral Source** | ✅ Pass | No existing behavior changes (FR-009). All existing modules (IR, WiFi, display, NVS, HTTP) unchanged. |
| **III. Credentials-at-Build** | ✅ Pass | `MICROPY_HEAP_SIZE` is non-sensitive. Heap buffer is a compile-time constant in firmware source, not a credential. |
| **IV. Backend Contract Compliance** | ✅ Pass | `badge.http_get/post` routes through the existing `BadgeAPI` C layer (FR-005). No new backend endpoints introduced. |
| **V. Reproducible Build** | ✅ Pass (with requirement) | MicroPython v1.27.0 must be pinned in `setup.sh` by URL/tag. `setup.sh` generates `micropython_embed/`; `build.sh` compiles it. Both scripts must be updated and the steps must be idempotent. |
| **VI. Hardware Safety** | ✅ Pass | No new GPIO assignments. Emergency chord uses existing BTN_UP (GPIO8) + BTN_DOWN (GPIO9). Escape uses FreeRTOS timer callback calling `mp_sched_keyboard_interrupt()` — no ISR, no new pins. eFuse untouched. |
| **VII. API Contract Library** | ✅ Pass | `badge.http_get/post` call the existing `BadgeAPI` C ABI via `extern "C"` bridge functions. The C extension (badge_mp/*.c) never touches `HTTPClient` directly — the C layer is the implementation, the Python layer is bindings only. |

### Complexity Tracking

*No violations requiring complexity tracking. The embedded scripting surface is now explicitly permitted under constitution v2.4.0 Principle I.*

---

## Project Structure

### Documentation (this feature)

```text
specs/007-embed-micropython-runtime/
├── plan.md              # This file
├── research.md          # Port selection, build integration, API decisions
├── data-model.md        # Entities, state transitions, mpconfigport flags
├── quickstart.md        # Firmware developer and app developer guides
├── contracts/
│   ├── badge-module-api.md       # badge Python module contract (v1)
│   └── app-filesystem-layout.md  # /apps/ directory layout on VFS
└── tasks.md             # Phase 2 output (/speckit.tasks — NOT created here)
```

### Source Code

New files in `firmware/Firmware-0308-modular/`:

```text
firmware/Firmware-0308-modular/
├── badge_mp/                       # NEW — badge C extension sources (C, not C++)
│   ├── mpconfigport.h              # MicroPython port config (feature flags, heap size)
│   ├── badge_module.c              # Top-level module: display sub-obj, input, gc, exit, constants
│   ├── badge_ir_mp.c               # badge.ir_send/available/read
│   ├── badge_http_mp.c             # badge.http_get/post
│   ├── badge_input_mp.c            # badge.button_pressed, pin_read/write, adc_read, tilt_read
│   └── BadgePython_bridges.h       # extern "C" bridge declarations (C++ → C crossing point)
├── BadgePython.h                   # NEW — Python launcher interface
├── BadgePython.cpp                 # NEW — VM lifecycle, escape chord timer, error handling
├── apps/                           # NEW — Python app source files (compiled + uploaded at flash time)
│   └── hello.py                    # Example/starter app
├── micropython_embed/              # GENERATED by setup.sh — gitignored
│   └── [generated .c/.h files]
├── BadgeConfig.h.example           # UPDATED — add MICROPY_HEAP_SIZE, MP_SCRIPT_MAX_BYTES
├── setup.sh                        # UPDATED — download MicroPython, generate embed sources
└── build.sh                        # UPDATED — compile micropython_embed/ as additional sources
```

Modified files:
- `Firmware-0308-modular.ino` — call `BadgePython::init()` in `setup()`, add Python app launch from menu
- `BadgeMenu.h` / `BadgeMenu.cpp` — add "Apps" menu item; app sub-menu lists `/apps/*.py`

**Structure Decision**: Single Arduino sketch project. Generated MicroPython embed sources in `micropython_embed/` (gitignored); authored C extension in `badge_mp/` (committed); C++ launcher in `BadgePython.{h,cpp}` (committed). No new top-level directories outside `firmware/`.
