pjerus/Temporal-Replay-26-Badge/specs/007-embed-micropython-runtime/spec.md

# Feature Specification: Embed MicroPython Scripting Runtime

**Feature Branch**: `007-embed-micropython-runtime`
**Created**: 2026-03-13
**Status**: Draft
**Input**: User description: "Embed MicroPython as a scripting runtime component inside the Arduino C++ firmware (firmware/Firmware-0308-modular/). The C++ firmware remains the host OS — MicroPython is initialized once during the boot sequence (while WiFi is connecting) and soft-reset between app launches. Target: ESP32-S3-MINI-1, Arduino ESP32 core 3.x on top of ESP-IDF 5.x. The interpreter must coexist with the existing FreeRTOS dual-core setup (IR task on Core 0, display/input on Core 1). MicroPython runs on Core 1. The display mutex must be respected when apps call display functions. Apps are loaded from the badge filesystem via mp_embed_exec_file or equivalent. The build system (build.sh/setup.sh) must be updated to include MicroPython as a dependency. No existing firmware behavior changes."

## User Scenarios & Testing *(mandatory)*

### User Story 1 - Python App Executes on Badge (Priority: P1)

A badge developer writes a Python script, copies it onto the badge filesystem, and selects it from the menu. The script runs to completion — drawing to the display, reading buttons, or doing simple logic — and when it exits the badge returns cleanly to the main menu.

**Why this priority**: This is the core value of the entire feature. Without a Python app running end-to-end, nothing else matters.

**Independent Test**: Copy a minimal "Hello, World" Python script to the badge filesystem, select it from the menu, and confirm the badge displays expected output then returns to the menu. Requires no other feature work.

**Acceptance Scenarios**:
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
