pjerus/Temporal-Replay-26-Badge/assets/credits/preview/aask_64.png

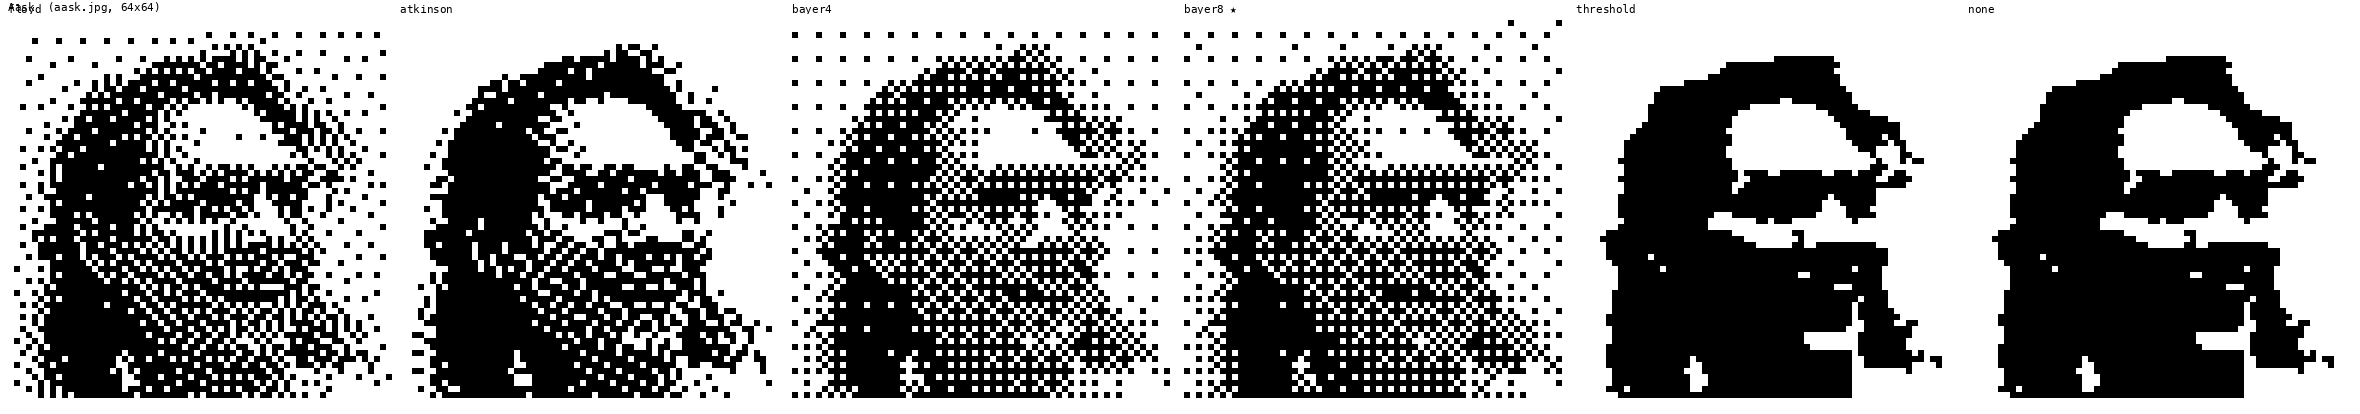
assets/credits/preview/aask_64.png
