pjerus/Temporal-Replay-26-Badge/assets/credits/preview/alex_64.png

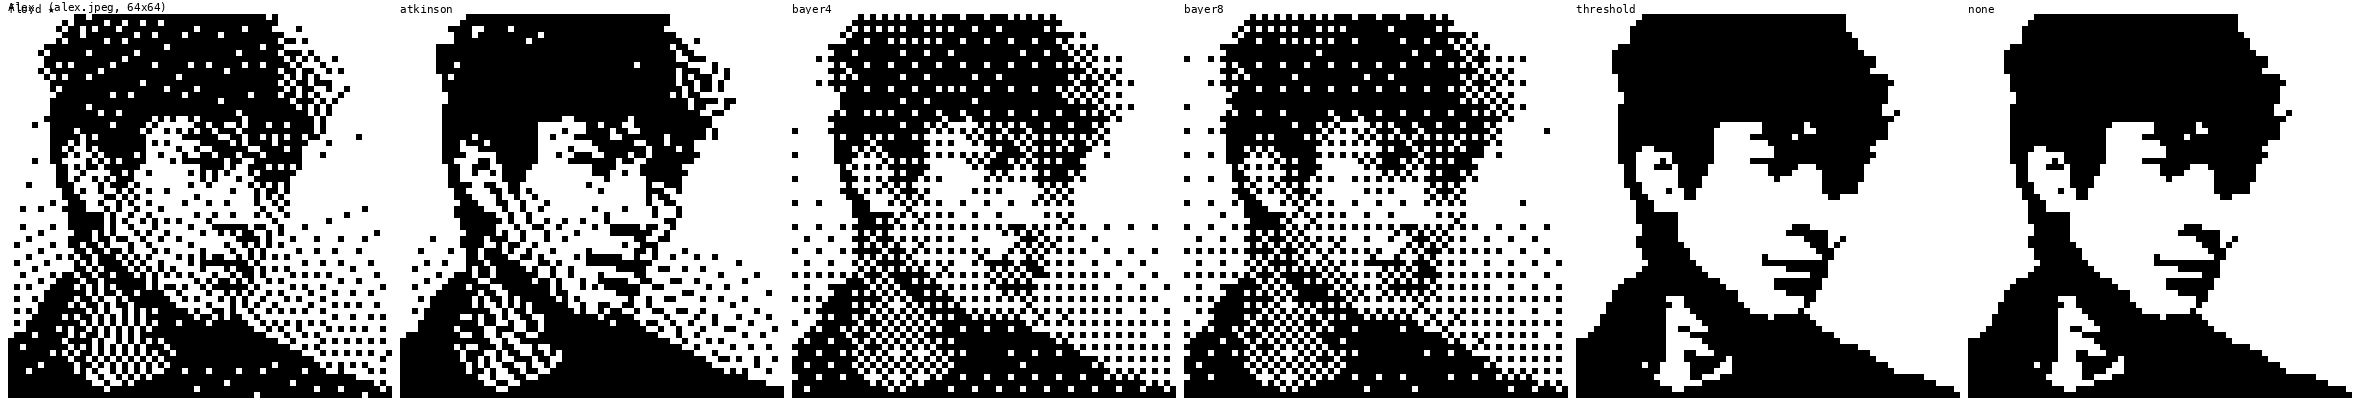
assets/credits/preview/alex_64.png
