pjerus/Temporal-Replay-26-Badge/assets/credits/preview/edward_64.png

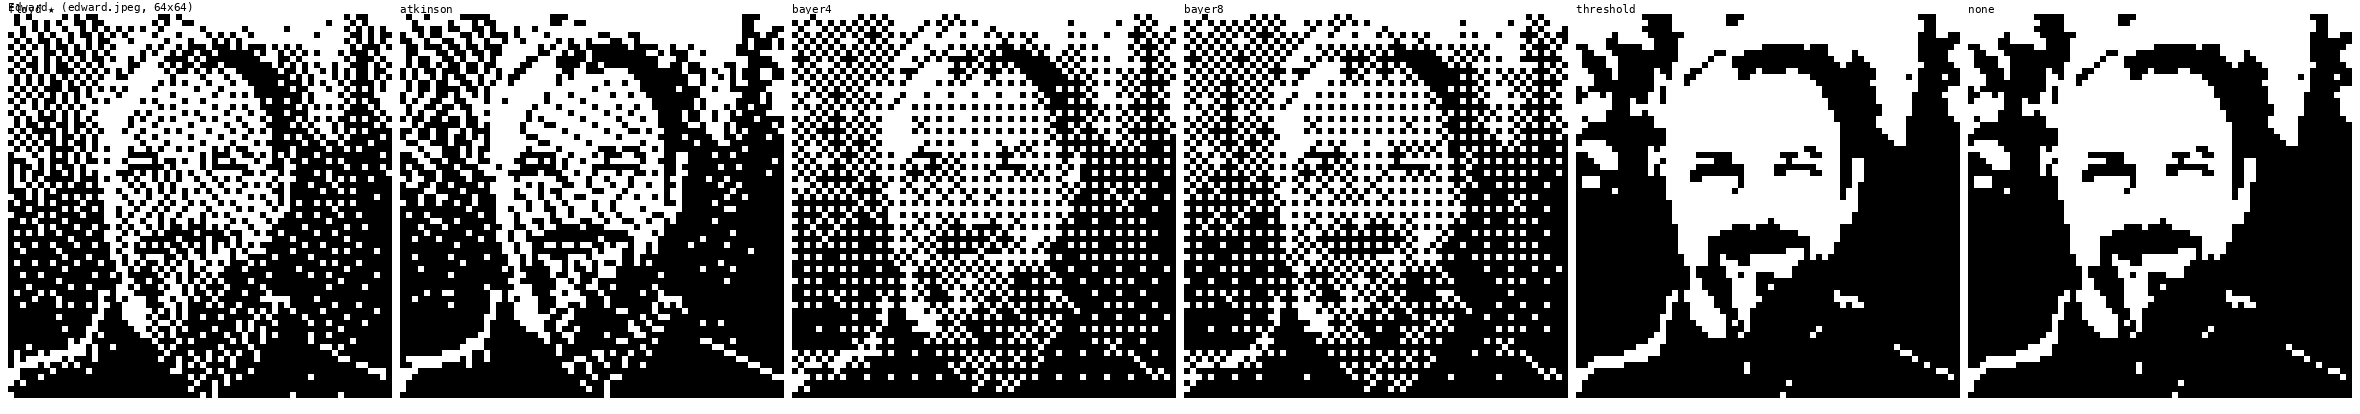
assets/credits/preview/edward_64.png
