pjerus/Temporal-Replay-26-Badge/assets/credits/preview/kev_64.png

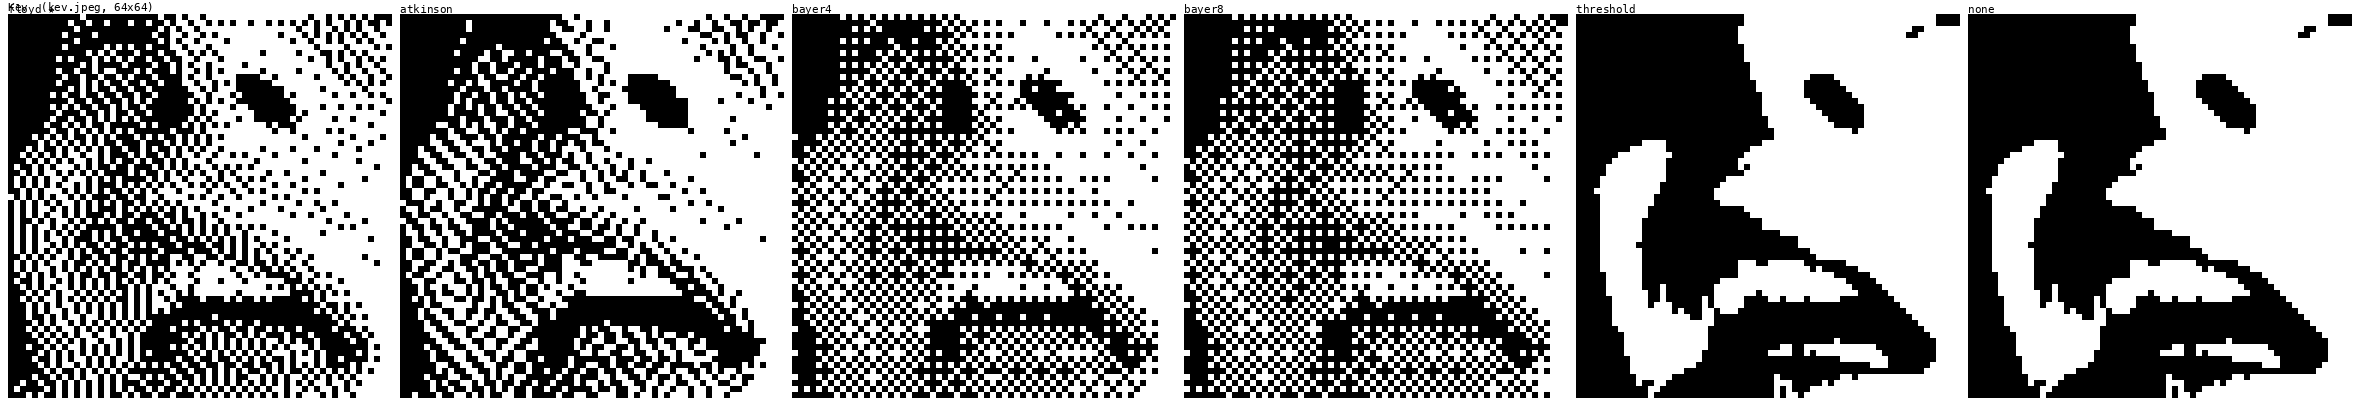
assets/credits/preview/kev_64.png
