pjerus/Temporal-Replay-26-Badge/assets/credits/preview/kevin2_64.png

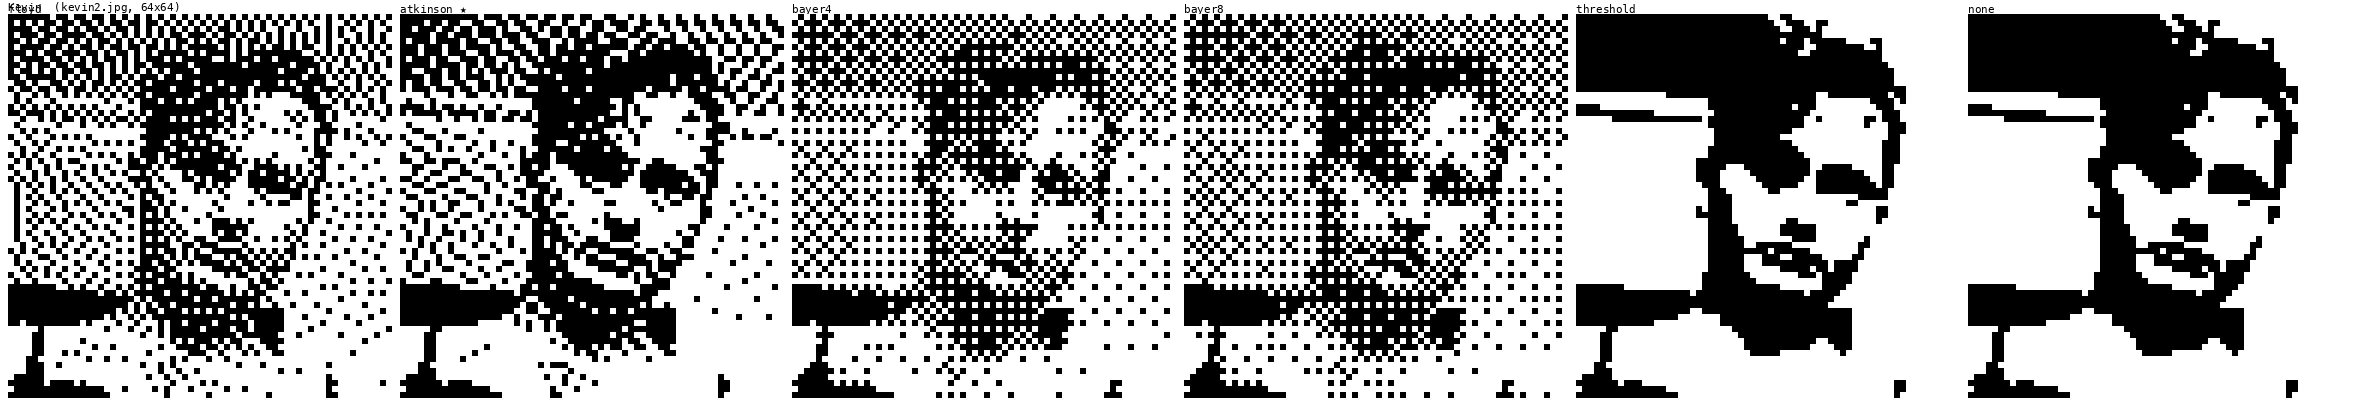
assets/credits/preview/kevin2_64.png
