pjerus/Temporal-Replay-26-Badge/assets/credits/preview/kevin3_64.png

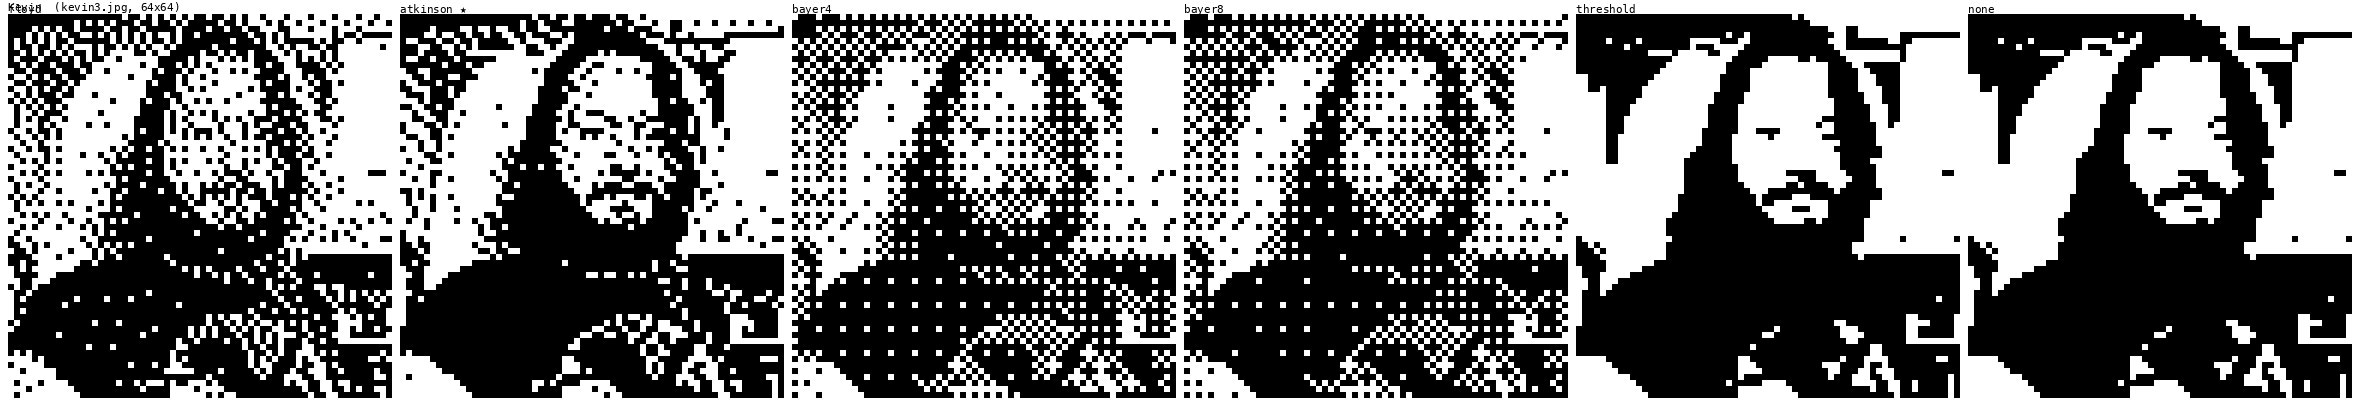
assets/credits/preview/kevin3_64.png
