pjerus/Temporal-Replay-26-Badge/assets/credits/preview/kevin_0_64.png

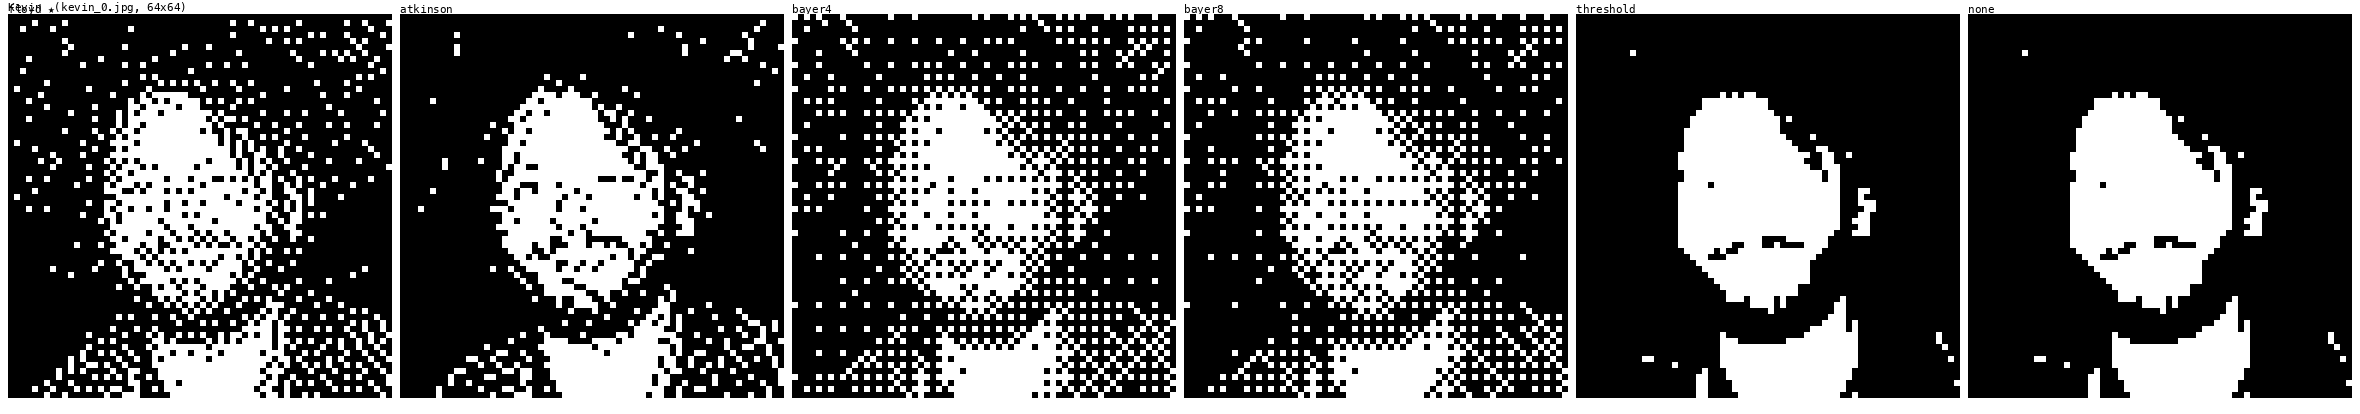
assets/credits/preview/kevin_0_64.png
