pjerus/Temporal-Replay-26-Badge/assets/credits/preview/kevin_1_64.png

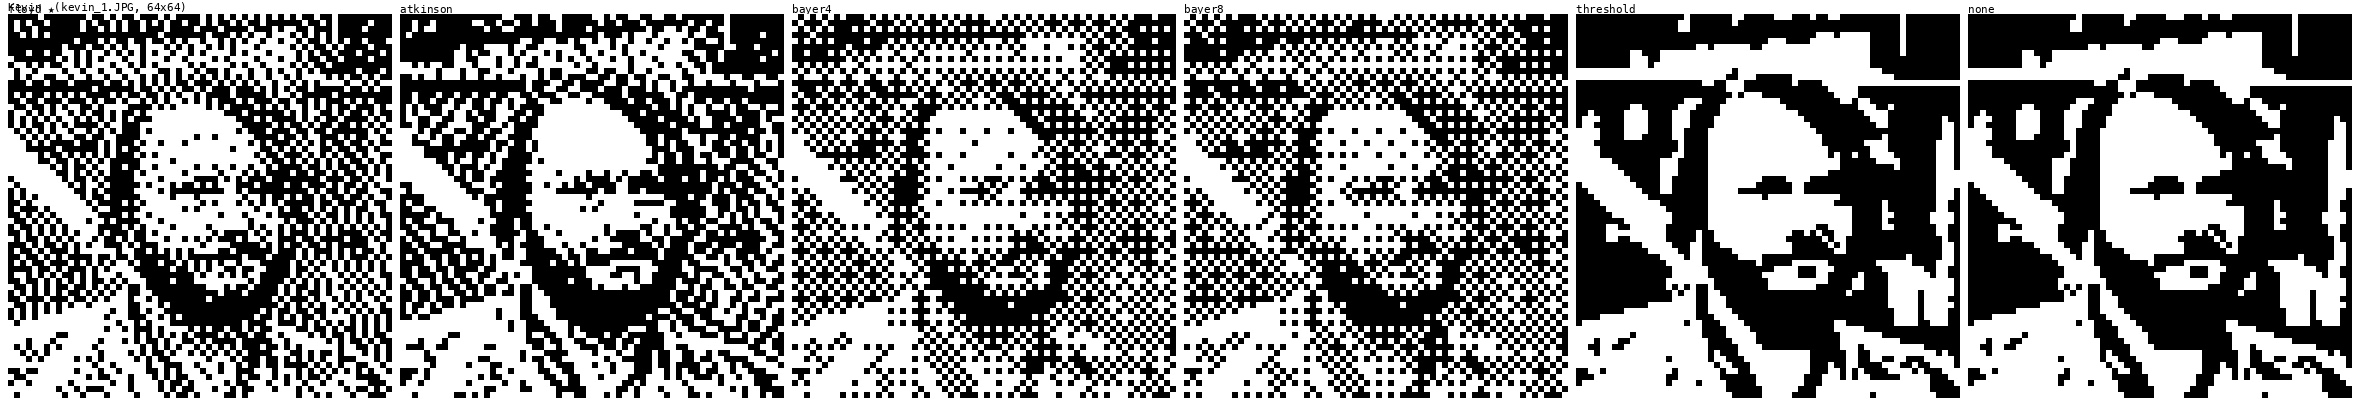
assets/credits/preview/kevin_1_64.png
