pjerus/Temporal-Replay-26-Badge/assets/credits/preview/shy2_64.png

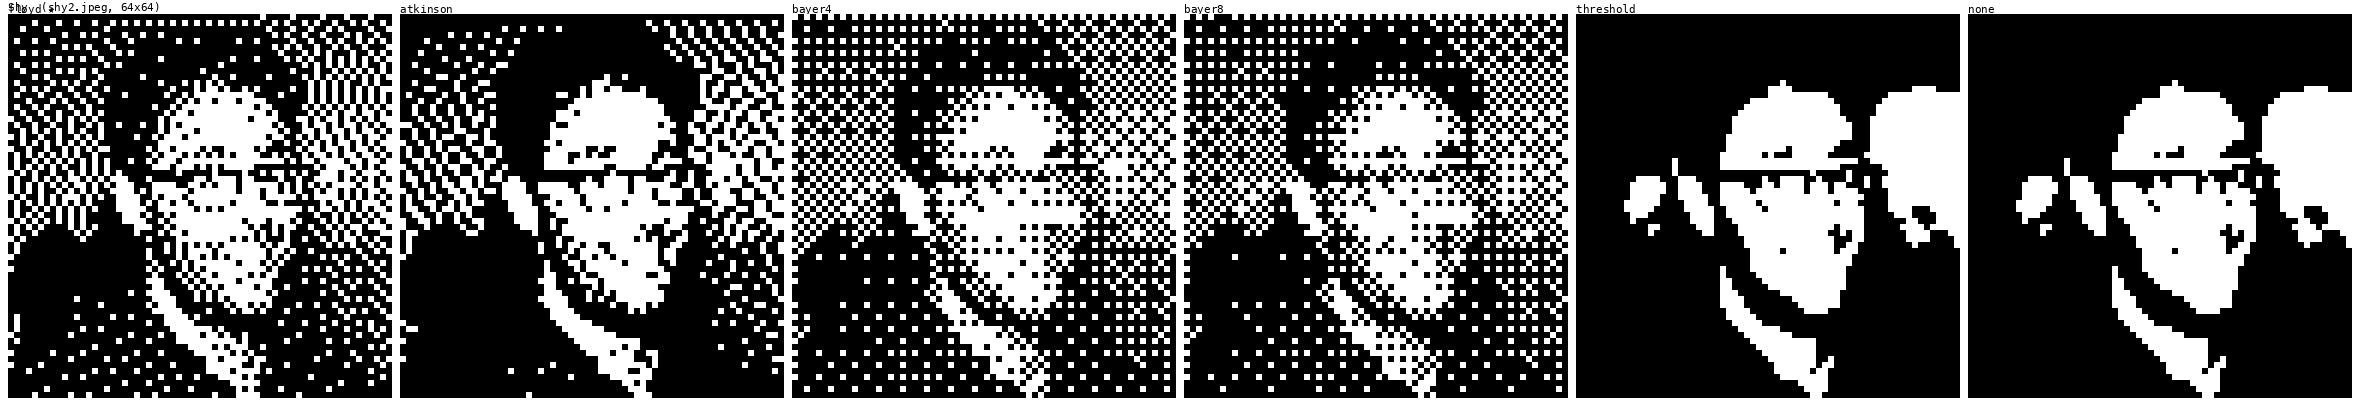
assets/credits/preview/shy2_64.png
