pjerus/Temporal-Replay-26-Badge/assets/credits/preview/shy_64.png

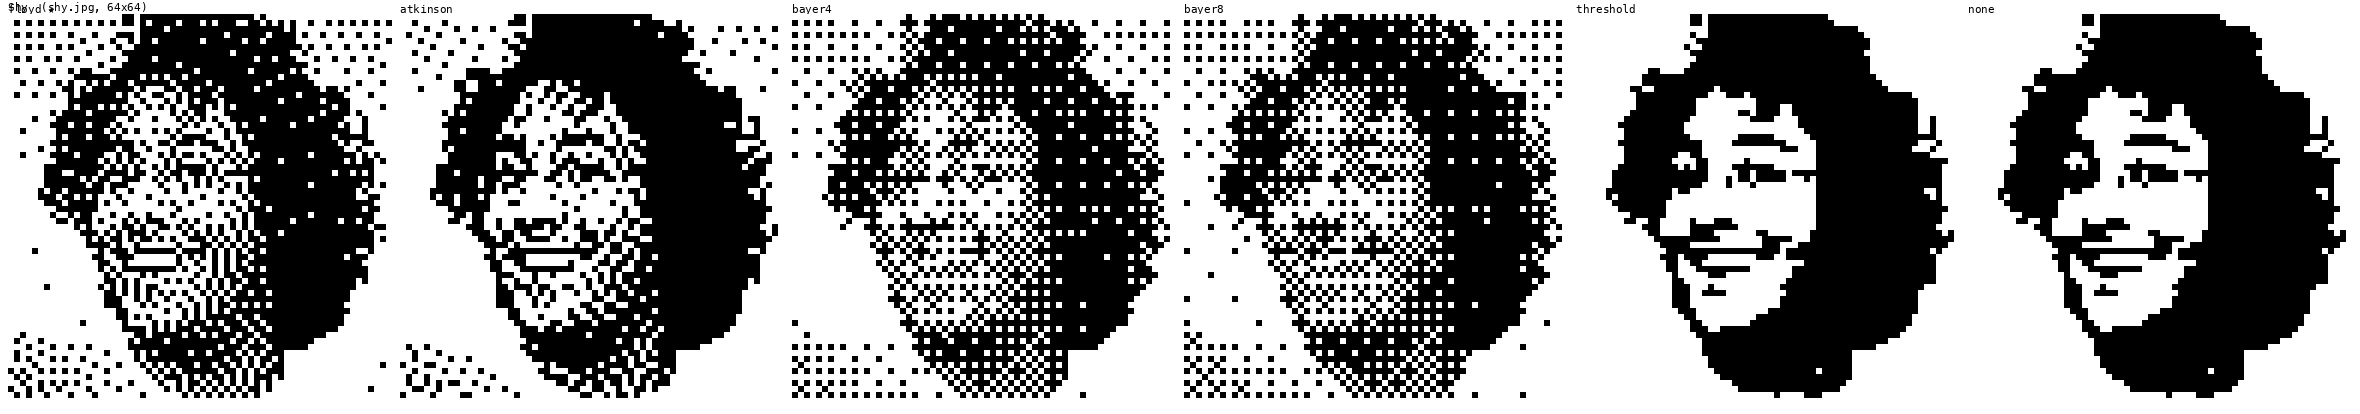
assets/credits/preview/shy_64.png
