pjerus/Temporal-Replay-26-Badge/assets/Rough-Enclosure.png

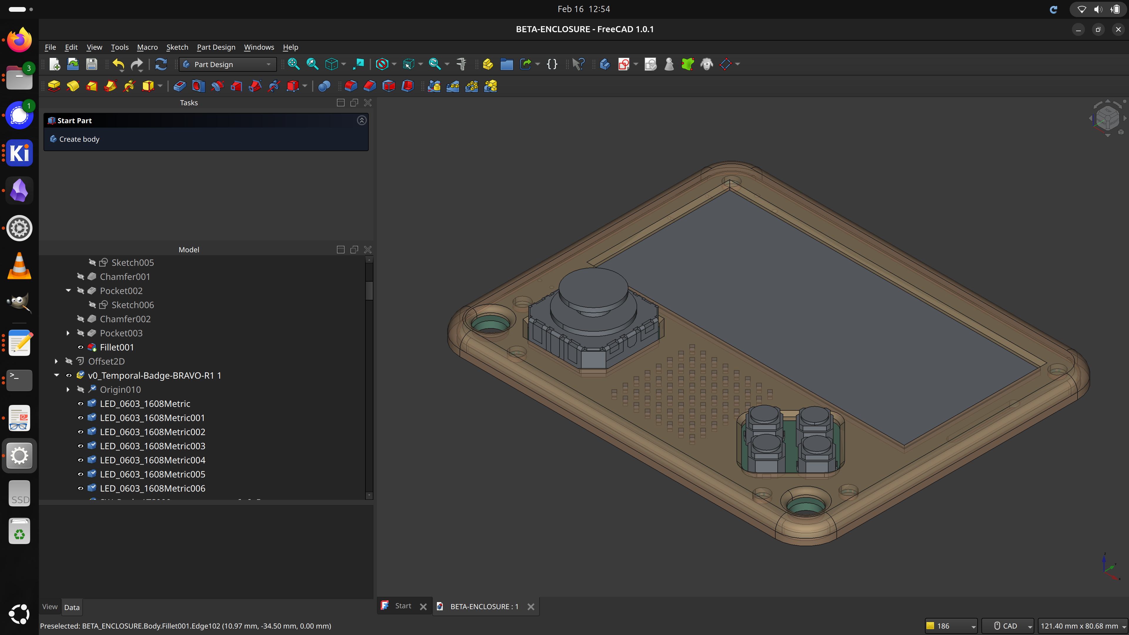
assets/Rough-Enclosure.png
