pjerus/Temporal-Replay-26-Badge/assets/Zig-moji/Animated/Ziggy-blink/128x128/Ziggy-blink-01-128x128.png

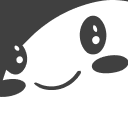
assets/Zig-moji/Animated/Ziggy-blink/128x128/Ziggy-blink-01-128x128.png
