pjerus/Temporal-Replay-26-Badge/assets/Zig-moji/Animated/Ziggy-fly/128x128/Ziggy-fly-03-128x128.png

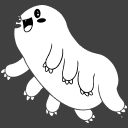
assets/Zig-moji/Animated/Ziggy-fly/128x128/Ziggy-fly-03-128x128.png
