pjerus/Temporal-Replay-26-Badge/assets/Zig-moji/Animated/Ziggy-heart/128x128/Ziggy-heart-03-128x128.png

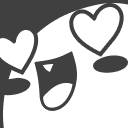
assets/Zig-moji/Animated/Ziggy-heart/128x128/Ziggy-heart-03-128x128.png
