pjerus/Temporal-Replay-26-Badge/assets/Zig-moji/Animated/Ziggy-sleep/128x128/Ziggy-sleep-01-128x128.png

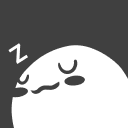
assets/Zig-moji/Animated/Ziggy-sleep/128x128/Ziggy-sleep-01-128x128.png
