pjerus/Temporal-Replay-26-Badge/assets/Zig-moji/Animated/Ziggy-wow/128x128/ziggy-head-wow-01-128x128.png

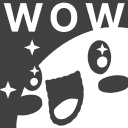
assets/Zig-moji/Animated/Ziggy-wow/128x128/ziggy-head-wow-01-128x128.png
