pjerus/Temporal-Replay-26-Badge/docs/t9-mockup-0.png

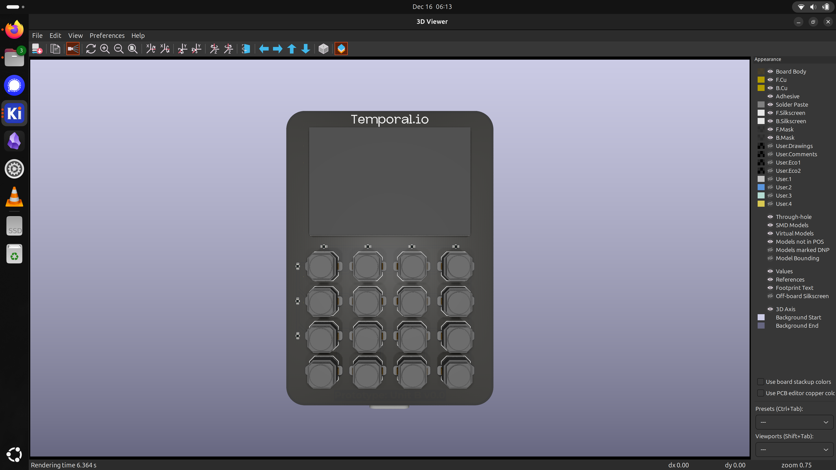
docs/t9-mockup-0.png
