pjerus/Temporal-Replay-26-Badge/docs/t9-mockup-1.png

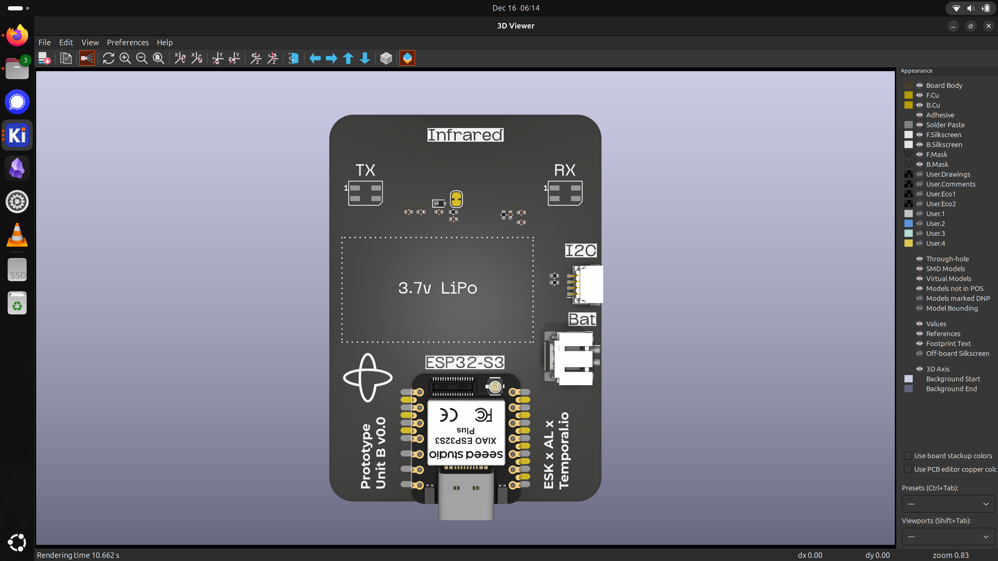
docs/t9-mockup-1.png
