pjerus/Temporal-Replay-26-Badge/docs/v0_Base-Prototype.png

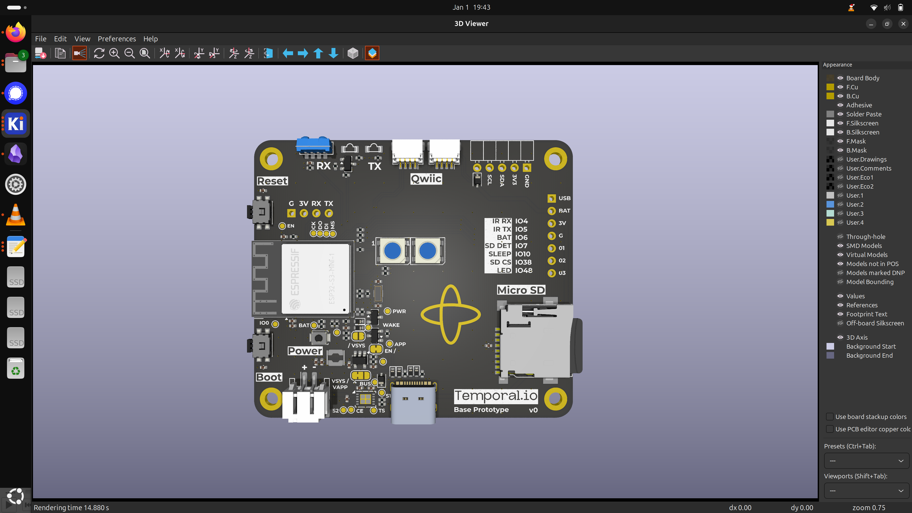
docs/v0_Base-Prototype.png
