pjerus/Temporal-Replay-26-Badge/hardware/CHARLIE/export/V0-Temporal-CHARLIE_Front.png

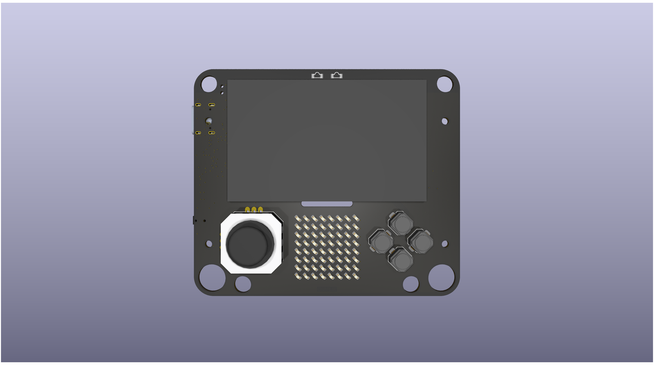
hardware/CHARLIE/export/V0-Temporal-CHARLIE_Front.png
