pjerus/Temporal-Replay-26-Badge/assets/ST7305.step

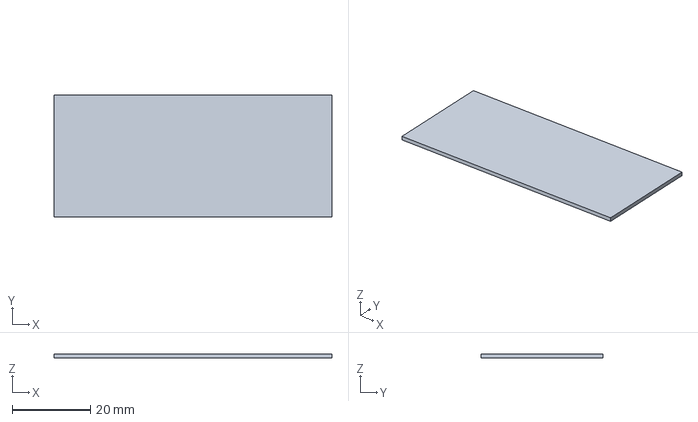
[picture p51: CAD file, 2026-05-07]
assets/ST7305.step
71.0 x 31.1 x 1.10 mm
