pjerus/Temporal-Replay-26-Badge/hardware/BRAVO/assets/v0_Temporal-Badge-BRAVO-R1.step

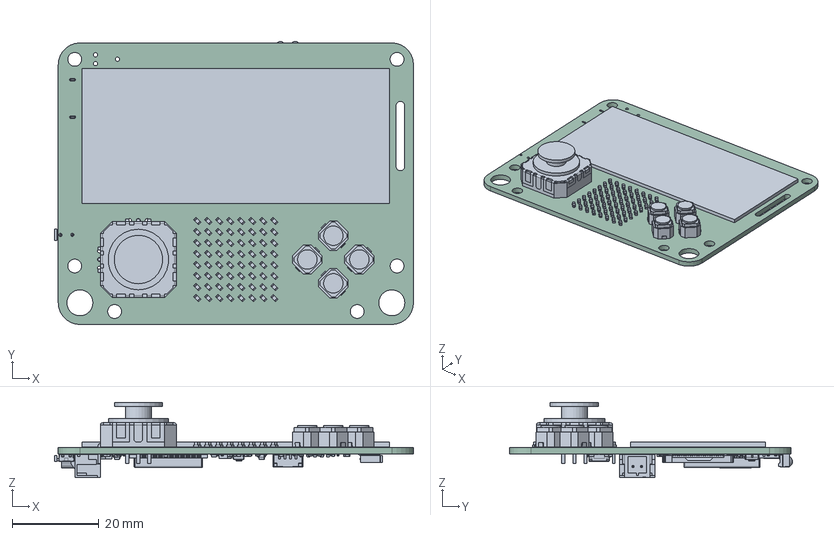
[picture p52: CAD file, 2026-05-07]
hardware/BRAVO/assets/v0_Temporal-Badge-BRAVO-R1.step
82.9 x 65.3 x 17.4 mm
LED_0603_1608Metric x 64
pin_1 x 4
pin_2 x 4
P2765
FPC-24
ST7305
R_0402_1005Metric x 36
C_0402_1005Metric x 32
SOT-23 x 2
Panasonic_EVQPUM_EVQPUD
D_SOD-523 x 8
R_0201_0603Metric x 8
ESP32-S3-WROOM-1
SOT-143
JST - PH - SMD (R) - 2Pin - 2.00mm
56F6E7FA-7C16-416F-93ED-149845DA8218
56F6E7FA-7C16-416F-93ED-149845DA8219
56F6E7FA-7C16-416F-93ED-149845DA8220
56F6E7FA-7C16-416F-93ED-149845DA8221
56F6E7FA-7C16-416F-93ED-149845DA8222
56F6E7FA-7C16-416F-93ED-149845DA8223
56F6E7FA-7C16-416F-93ED-149845DA8224
56F6E7FA-7C16-416F-93ED-149845DA8225
56F6E7FA-7C16-416F-93ED-149845DA8226
56F6E7FA-7C16-416F-93ED-149845DA8227
56F6E7FA-7C16-416F-93ED-149845DA8228
SW_SPST_B3U-1000P-B
SOT-23-5
Crystal_SMD_3215-2Pin_3.2x1.5mm
USB-C
LGA-12_2x2mm_P0.5mm
D_SOD-123F
82672Heimdall
Temporal-Badge-BRAVO_PCB
