pjerus/Temporal-Replay-26-Badge/assets/Temporal-Badge.step

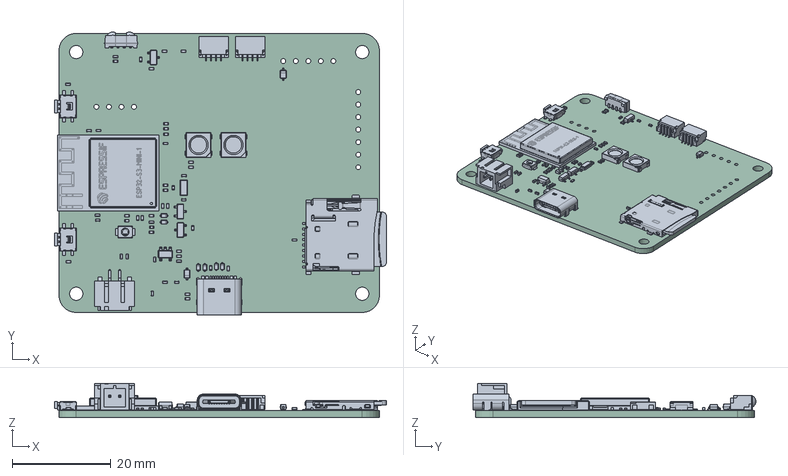
[picture p53: CAD file, 2026-05-07]
assets/Temporal-Badge.step
67.3 x 57.4 x 6.98 mm
D_SOD-523 x 6
C_0402_1005Metric x 17
R_0402_1005Metric x 31
SM4B-SRSS-TB x 2
SOT-23 x 3
SW_SPST_B3U-1000P-B
LED_WS2812B_PLCC4_5.0x5.0mm_P3.2mm x 2
Panasonic_EVQPUL_EVQPUC x 2
JST - PH - SMD (R) - 2Pin - 2.00mm
D_SOD-323 x 2
ESP32-S3-MINI-1
SOT-23-5
Crystal_SMD_3215-2Pin_3.2x1.5mm
Case^MicroSD_Socket
Insert^MicroSD_Socket
Brace^MicroSD_Socket
Spring^MicroSD_Socket
Lid^MicroSD_Socket
Pin_Middle^MicroSD_Socket x 5
Pin_Short^MicroSD_Socket
Pin_Long^MicroSD_Socket x 2
MicroSD_Card^MicroSD_Socket
Pin_CardIn^MicroSD_Socket
USB-C
82672Heimdall
Temporal-Badge_PCB
