pjerus/Temporal-Replay-26-Badge/hardware/CHARLIE/assets/V0-CHARLIE_PCB-Outline-R1.dxf

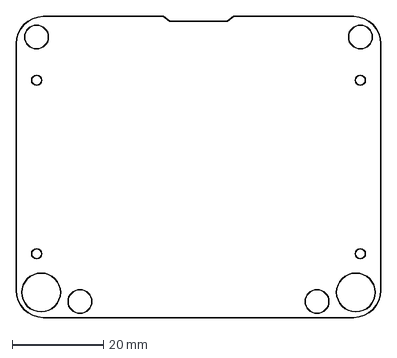
[picture p55: CAD file, 2026-05-07]
hardware/CHARLIE/assets/V0-CHARLIE_PCB-Outline-R1.dxf
80.0 x 66.0 mm
