pjerus/Temporal-Replay-26-Badge/assets/OLED 2.42 V1.1 SSD1309.STEP

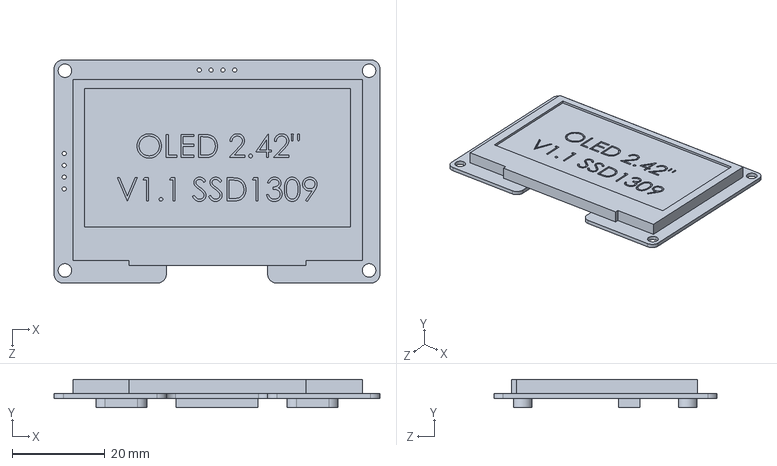
[picture p56: CAD file, 2026-05-07]
assets/OLED 2.42 V1.1 SSD1309.STEP
70.2 x 6.10 x 48.1 mm
