pjerus/Temporal-Replay-26-Badge/hardware/BRAVO/assets/BRAVO-Outline-R2.dxf

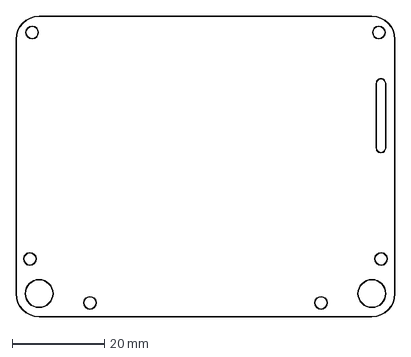
[picture p57: CAD file, 2026-05-07]
hardware/BRAVO/assets/BRAVO-Outline-R2.dxf
82.0 x 65.0 mm
