pjerus/Temporal-Replay-26-Badge/hardware/BRAVO/assets/BRAVO-Outline-R3.dxf

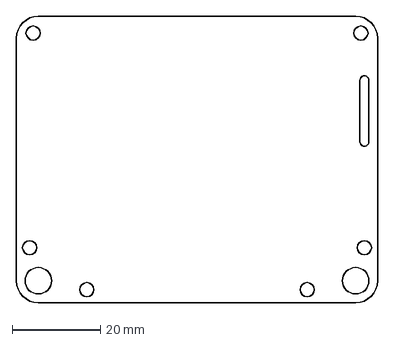
[picture p59: CAD file, 2026-05-07]
hardware/BRAVO/assets/BRAVO-Outline-R3.dxf
82.0 x 65.0 mm
