pjerus/Temporal-Replay-26-Badge/ignition/flash_worker/workflows.py

"""Temporal workflows for badge build and flash operations."""
import asyncio
import re
from datetime import timedelta

from temporalio import workflow
from temporalio.common import RetryPolicy

with workflow.unsafe.imports_passed_through():
    from flash_worker.activities import (
        build_firmware,
        detect_badge_devices,
        detect_badge_ports,
        flash_badge_images,
        prepare_badge_devices_for_flashing,
        prepare_flash_artifacts,
        resolve_badge_port,
        verify_badge_boot_marker,
        verify_badge_ble,
    )

TASK_QUEUE = "badge-flash"
MAX_CONCURRENT_FLASHES = 32
FLASH_START_STAGGER_SECONDS = 0

_BUILD_RETRY  = RetryPolicy(maximum_attempts=1)   # builds are deterministic
_DETECT_RETRY = RetryPolicy(maximum_attempts=3)
_FLASH_RETRY  = RetryPolicy(
    maximum_attempts=3,
    initial_interval=timedelta(seconds=5),
    backoff_coefficient=2.0,
    maximum_interval=timedelta(seconds=30),
)
_VERIFY_RETRY = RetryPolicy(maximum_attempts=1)
_PREPARE_RETRY = RetryPolicy(maximum_attempts=1)
_ACTIVITY_ONCE = RetryPolicy(maximum_attempts=1)
_FLASH_ATTEMPTS = 3
_BOOT_ATTEMPTS = 2
_BLE_ATTEMPTS = 1


def _safe_id_part(value: str, fallback: str = "unknown") -> str:
    value = re.sub(r"[^A-Za-z0-9_.-]+", "-", value or "").strip("-")
    return (value or fallback)[:80]


def _badge_label(index: int) -> str:
    return f"Badge {index + 1:02d}"
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
